joachimth/mk2-reference-loudspeaker/assets/drawings/front_baffle.pdf

## Mk3 Front Baffle —

Cutout & Hole Layout Panel: 300 × 1180 mm, 22 mm birch

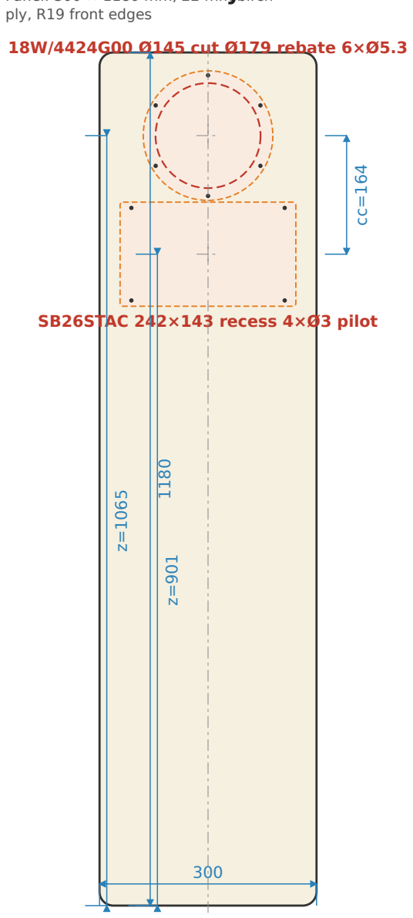
[picture p1: figure]
ply, R19 front edges; 18W/4424G00 Ø145 cut Ø179 rebate 6×Ø5.3; SB26STAC 242×143 recess 4×Ø3 pilot

Red dashed: cutout Orange: rebate Dots: pilot Ø3
