joachimth/mk2-reference-loudspeaker/assets/drawings/mk3-cabinet-drawings.pdf

## Mk3 Cabinet — Assembly Measurement Drawing

### FRONT

### SIDE

12SW

divider 19°

D=420

H=1180 520

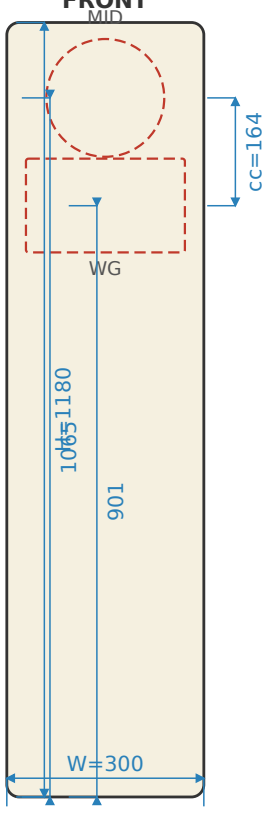
[picture p2: figure]
MID; W=300 H=¹¹⁸⁰ 1065

Internal: 256 × 376 × 1136 mm | Wall: 22 mm | Roundover: R19
Driver heights: MID z=1065 WG/TW z=901 Woofer z=520 | C-C mid/tw:
164 mm Shelf braces at z=[160, 330, 730] | Divider tilt: 19°

## Mk3 Cabinet — Panel Cut List

Material: 22 mm birch plywood | External: 300 × 420 × 1180 mm
Panel | Width (mm) Height/Depth (mm) | Qty | Thickness | Notes
Front baffle | 300 | 1180 | 1 | 22 | R19 front vertical edges, mid + WG cutouts
Back panel | 300 | 1180 | 1 | 22 | Square edges
Side panel L | 420 | 1180 | 1 | 22 | Woofer cutout Ø284, 8×Ø5.5 on Ø319 BCD
Side panel R | 420 | 1180 | 1 | 22 | Woofer cutout Ø284, 8×Ø5.5 on Ø319 BCD (opposed)
Top panel | 300 | 420 | 1 | 22 | Square edges
Bottom panel | 300 | 420 | 1 | 22 | Square edges
Divider plate | 300 | 420 | 1 | 22 | Tilted 19°, cut to fit cavity
Shelf brace 1 | 256 | 376 | 1 | 22 | Ring shelf, rim 45 mm, z=160
Shelf brace 2 | 256 | 376 | 1 | 22 | Ring shelf, rim 45 mm, z=330
Shelf brace 3 | 256 | 376 | 1 | 22 | Ring shelf, rim 45 mm, z=730
Total panels: 10 | Total panel area: 2.37 m² | Plywood volume: 0.05 L
NOTE: Divider plate and shelf braces are cut to fit the internal cavity (256 × 376 mm). Measure
actual internal dims before cutting. All dimensions from cabinet.scad (single source of truth). Verify driver cutouts against datasheet

## Mk3 Front Baffle —

Cutout & Hole Layout Panel: 300 × 1180 mm, 22 mm birch

ply, R19 front edges; 18W/4424G00 Ø145 cut Ø179 rebate 6×Ø5.3; SB26STAC 242×143 recess 4×Ø3 pilot

Red dashed: cutout Orange: rebate Dots: pilot Ø3

## Mk3 Side Panel — Woofer

Cutout & Hole Layout Panel: 420 × 1180 mm, 22 mm birch ply (flat,

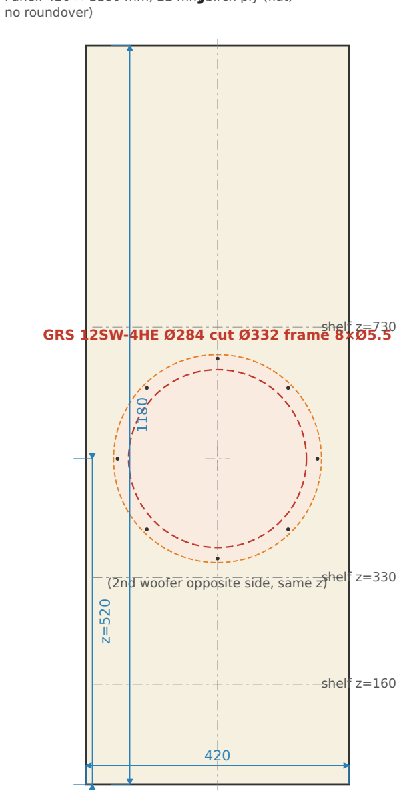
[picture p3: figure]
no roundover); GRS 12SW-4HE Ø284 cut Ø332 frame 8×Ø5.5; (2nd woofer opposite side, same z); shelf z=160; shelf z=330; shelf z=730

## Front Baffle — Cut

Drawing 300 × 1180 mm, 22 mm ply, R19 front edges

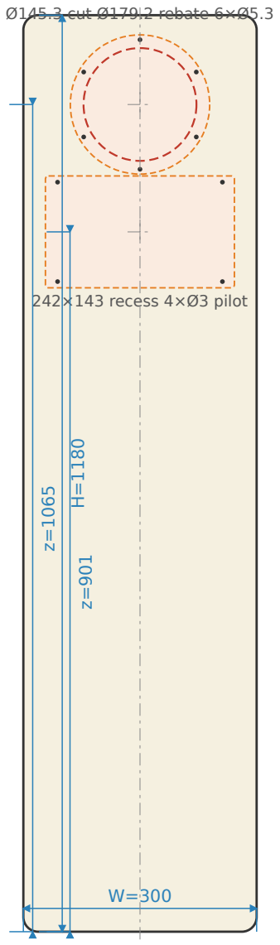
[picture p4: figure]
Ø145.3 cut Ø179.2 rebate 6×Ø5.3; 242×143 recess 4×Ø3 pilot

## Back Panel — Cut

Drawing 300 × 1180 mm, 22 mm ply, square edges

W=300

H=1180 No cutouts

## Side Panel LEFT — Cut

Drawing 420 × 1180 mm, 22 mm ply, woofer on left face

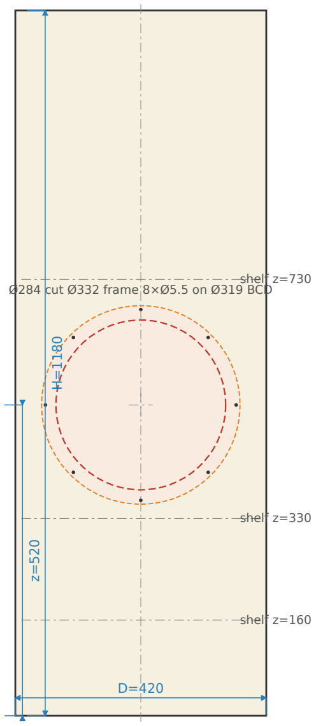
[picture p5: figure]
Ø284 cut Ø332 frame 8×Ø5.5 on Ø319 BCD; shelf z=160; shelf z=330; shelf z=730

## Side Panel RIGHT — Cut

Drawing 420 × 1180 mm, 22 mm ply, woofer on right (opposed) face

## Top Panel — Cut Drawing

300 × 420 mm, 22 mm ply, R19 front
edge

W=300

D=420 No cutouts

## Bottom Panel — Cut

Drawing 300 × 420 mm, 22 mm ply, R19 front edge

W=300

D=420 No cutouts

## Divider Plate — Cut

Drawing 256 × 376 mm, 22 mm ply, tilted 19° in cabinet

Cut to internal cavity shape (front edge follows rounded side walls)

Front edge sits at z=985 mm, rises 19° toward rear

int W=256 int D=³⁷⁶

tilt 19°

## Shelf Brace ×3 — Cut

Drawing Outer: 256 × 376 mm (internal cavity) Rim: 45 mm Thickness: 22 mm Qty: 3 (z=[160, 330, 730])

Open centre
166 × 286 mm

outer 256 outer 376

inner 166

## Skæreplan — massiv fyr 25 mm (Jem & Fix) — ET PAR

5× 620×2420×25 mm | 300×420×1180 mm | 2 kabinetter (V+H)

Side L (V)
420×1180 mm

Side L (H)
420×1180 mm

spild
60 mm

reserve
200 mm

Plade 1
sider V

Side R (V)
420×1180 mm

Side R (H)
420×1180 mm

spild
60 mm

reserve
200 mm

Plade 2
sider H

Front (V)
300×1180 mm

Front (H)
300×1180 mm

spild
60 mm

Divider (V)
trim→250×370

Hylde 1 (V)
trim→250×370

Hylde 2 (V)
trim→250×370

Hylde 3 (V)
trim→250×370

reserve
940 mm

Plade 3
front + div V + hylder V

Bagplade (V)
300×1180 mm

Bagplade (H)
300×1180 mm

spild
60 mm

Divider (H)
trim→250×370

Hylde 1 (H)
trim→250×370

Hylde 2 (H)
trim→250×370

Hylde 3 (H)
trim→250×370

reserve
940 mm

Plade 4
bagplade + div H + hylder H

Toplåg (V)
300×420 mm

Bundplade (V)
300×420 mm

Toplåg (H)
300×420 mm

Bundplade (H)
300×420 mm

reserve
740 mm

reserve
320 mm

Plade 5
toplåg + bund
Bruges | Reserve/spild | Rip-snit (orange)
