joachimth/mk2-reference-loudspeaker/assets/drawings/panel_front_baffle.pdf

## Front Baffle — Cut

Drawing 300 × 1180 mm, 22 mm ply, R19 front edges

Ø145.3 cut Ø179.2 rebate 6×Ø5.3; 242×143 recess 4×Ø3 pilot
