joachimth/mk2-reference-loudspeaker/assets/mk2_estimeret_respons.png

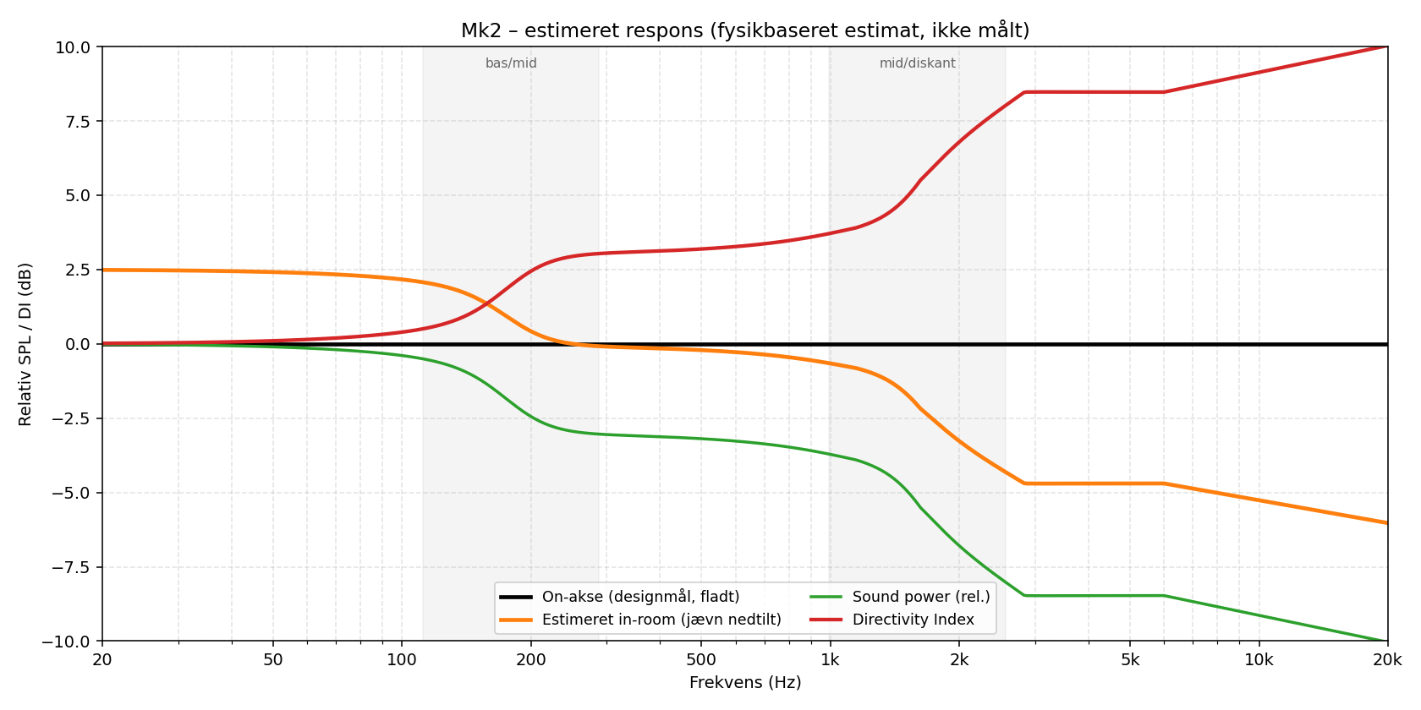
assets/mk2_estimeret_respons.png
