joachimth/mk2-reference-loudspeaker/assets/mk2_kabinet_tegning.png

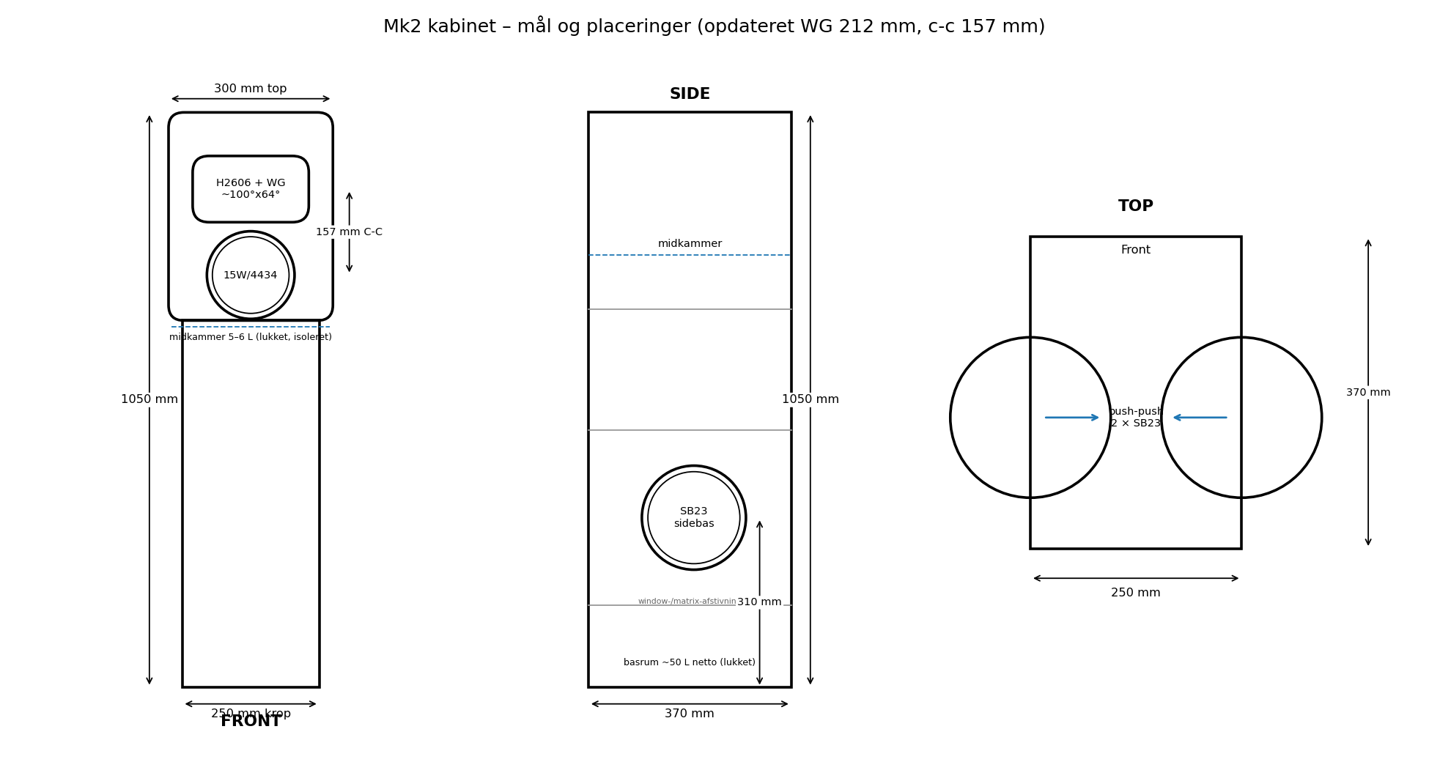
assets/mk2_kabinet_tegning.png
