joachimth/mk2-reference-loudspeaker/assets/renders/baffel_insert_fit_front.png

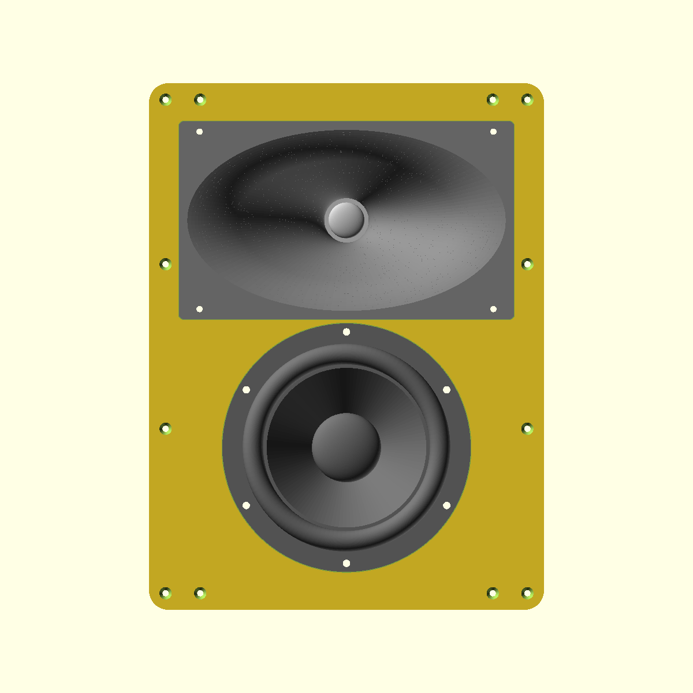
assets/renders/baffel_insert_fit_front.png
