joachimth/mk2-reference-loudspeaker/assets/renders/baffel_insert_fit_rear.png

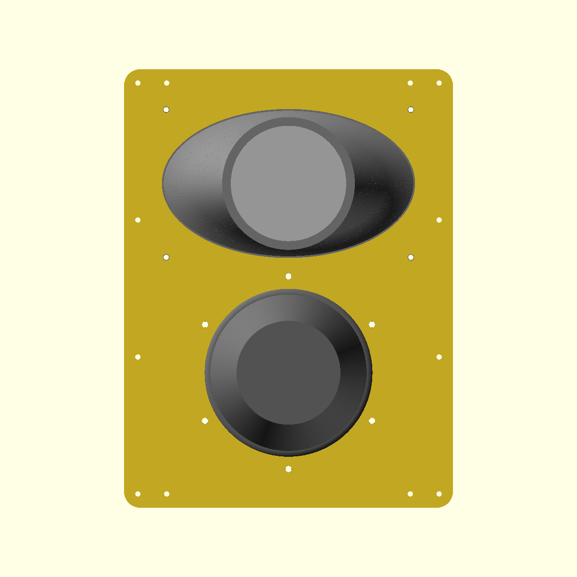
assets/renders/baffel_insert_fit_rear.png
