joachimth/mk2-reference-loudspeaker/assets/renders/baffel_insert_front.png

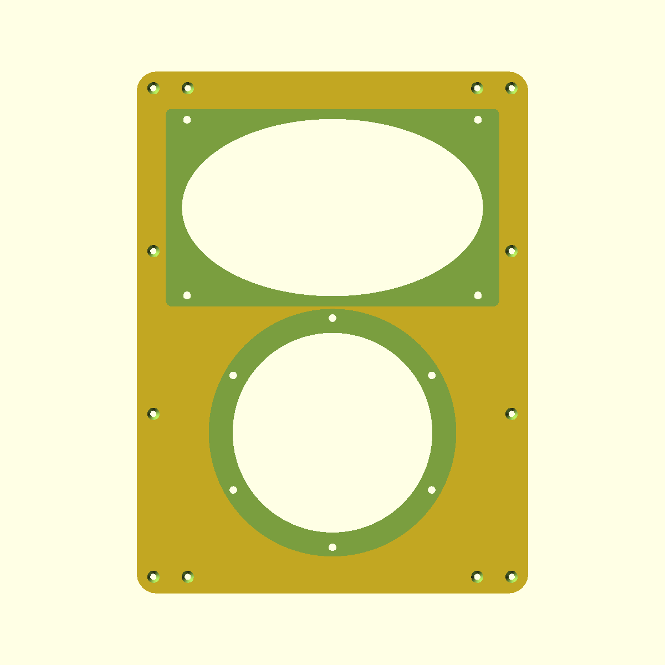
assets/renders/baffel_insert_front.png
