joachimth/mk2-reference-loudspeaker/assets/renders/cabinet_cutaway.png

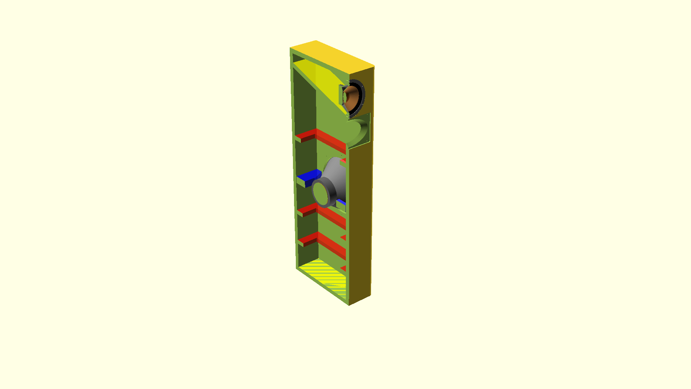
assets/renders/cabinet_cutaway.png
