joachimth/mk2-reference-loudspeaker/simulations/plots/bass_alignment_maxspl.png

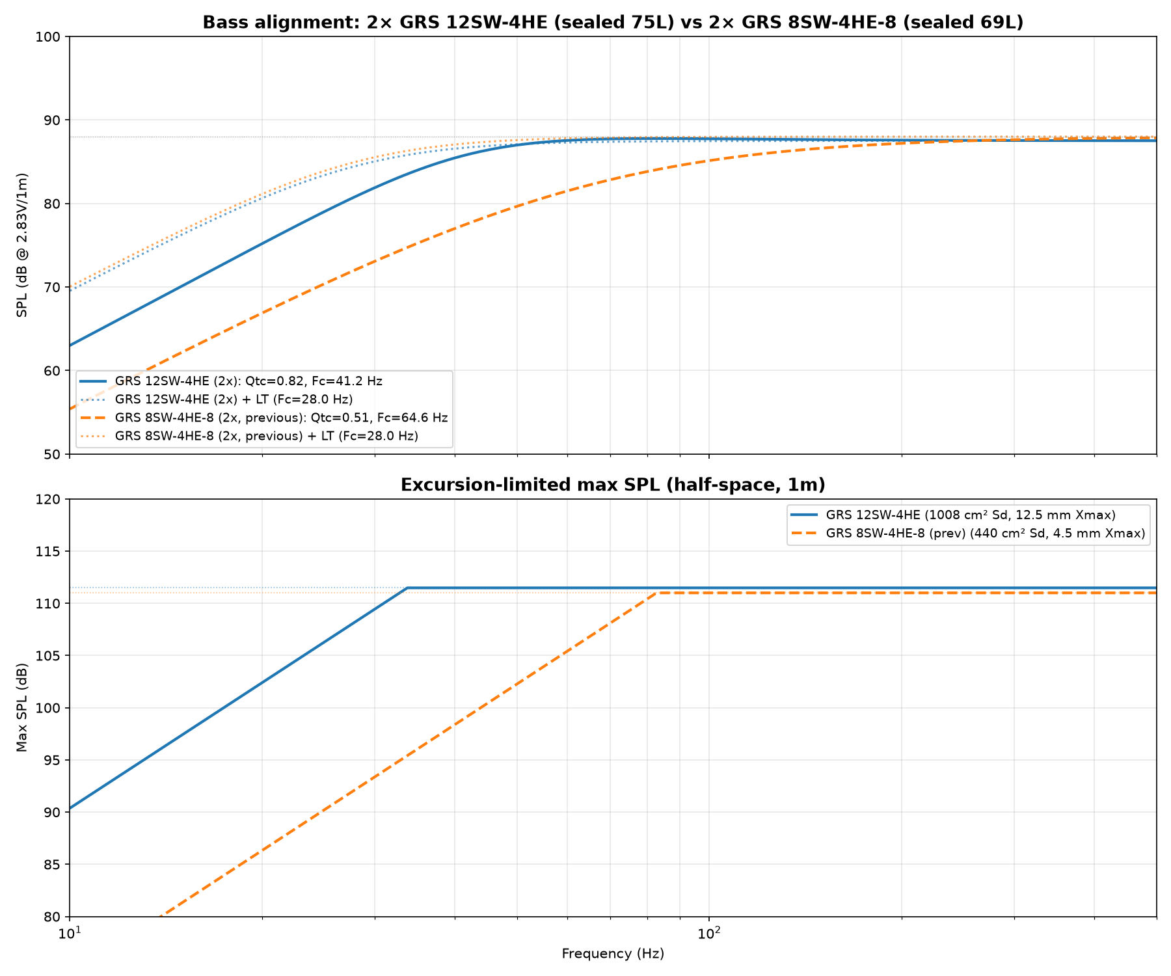
simulations/plots/bass_alignment_maxspl.png
