joachimth/mk2-reference-loudspeaker/simulations/plots/bass_volume_compare.png

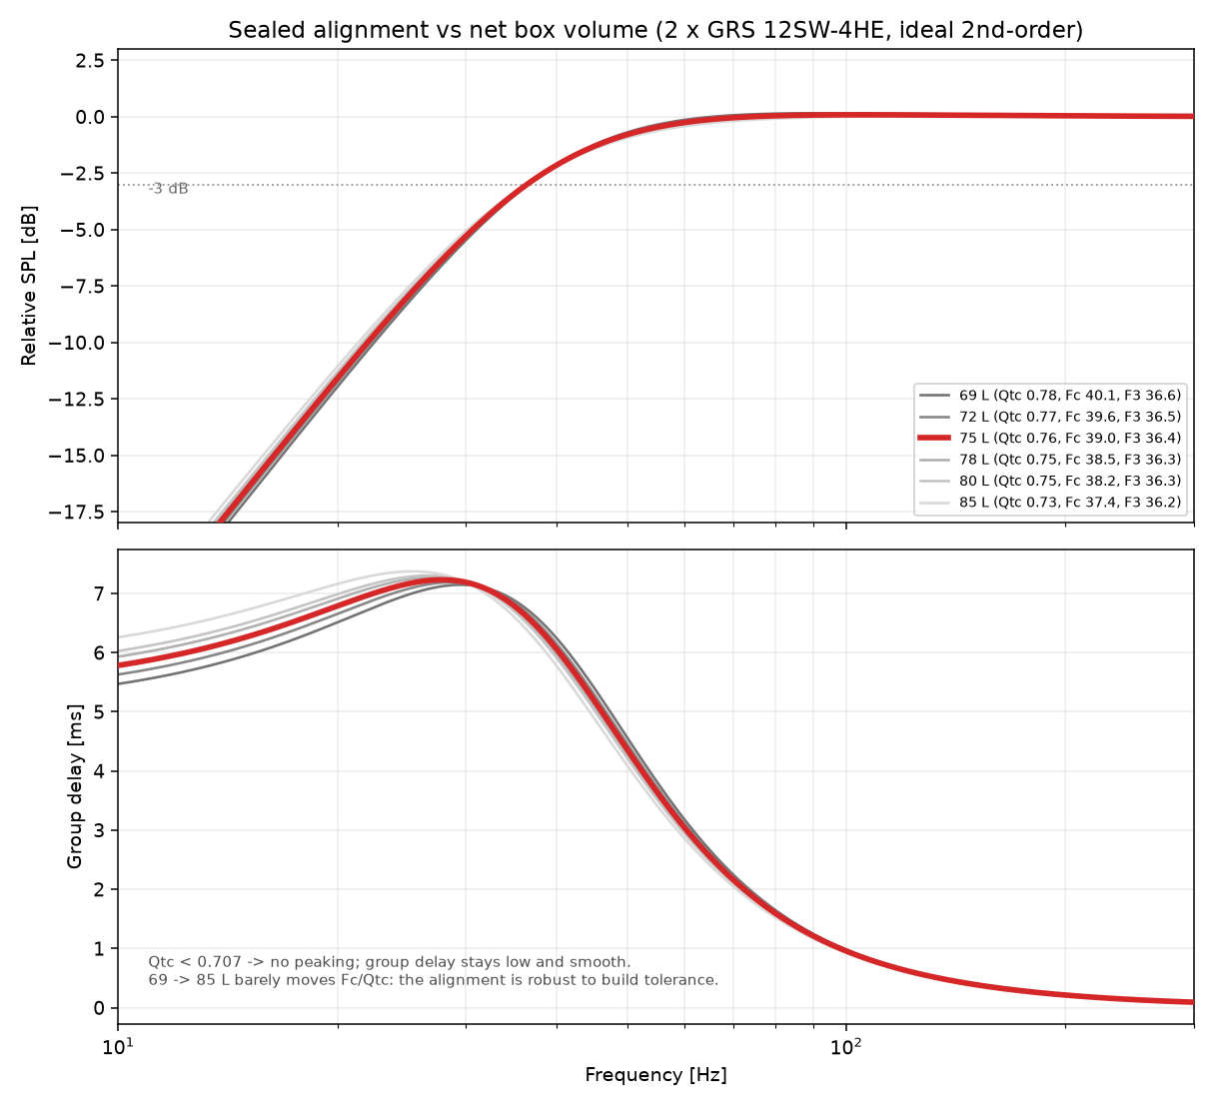
simulations/plots/bass_volume_compare.png
