joachimth/mk2-reference-loudspeaker/simulations/plots/breakin_projection.png

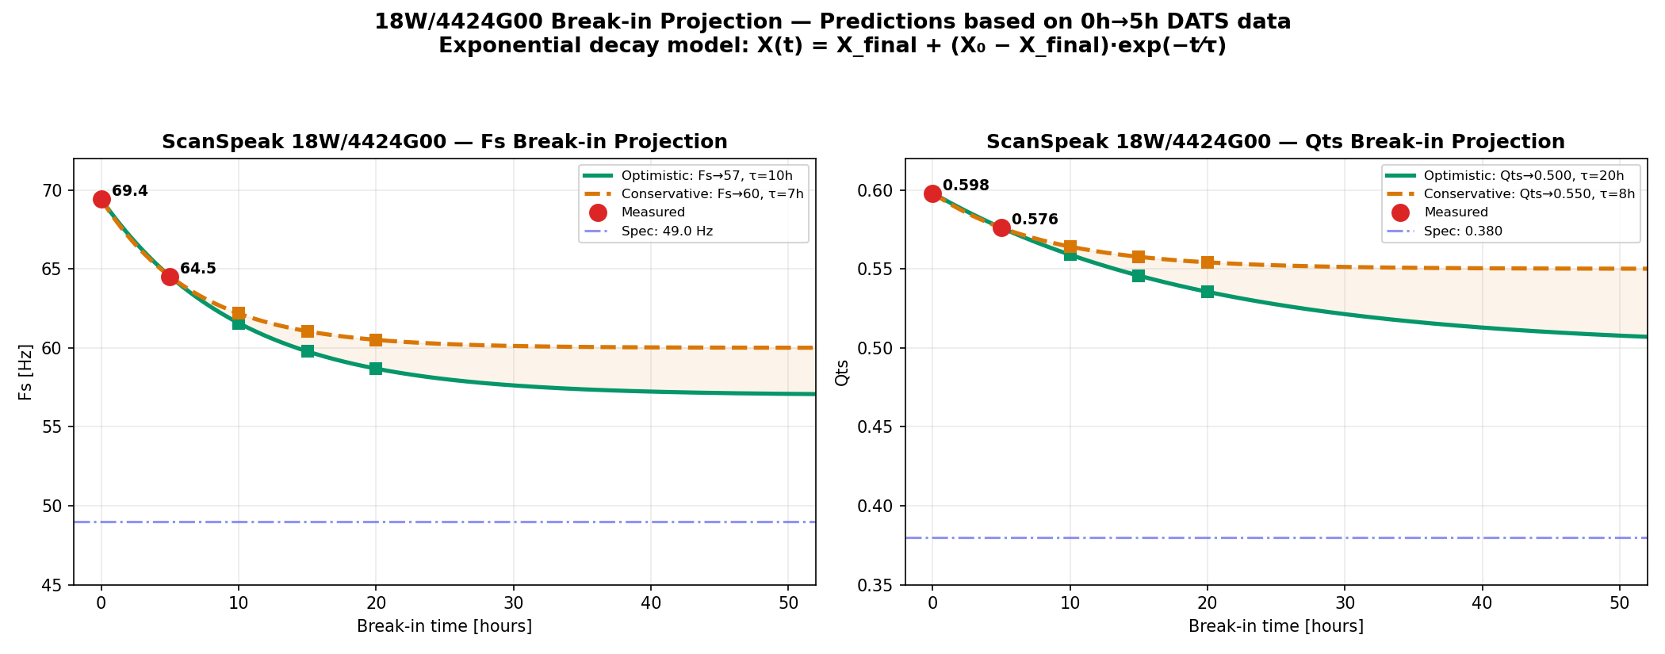
simulations/plots/breakin_projection.png
