joachimth/mk2-reference-loudspeaker/simulations/plots/crossover_optimization.png

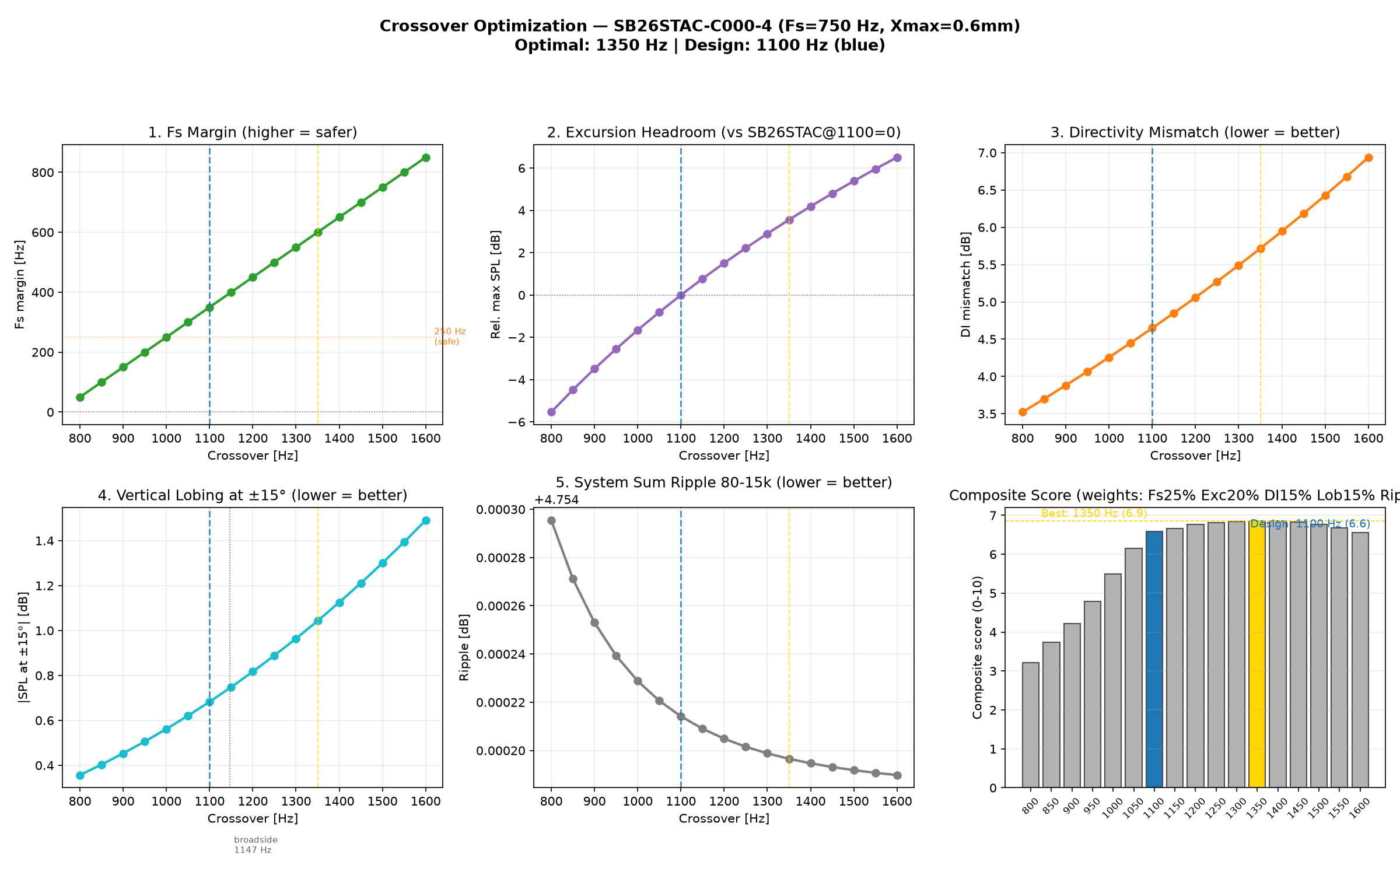
simulations/plots/crossover_optimization.png
