joachimth/mk2-reference-loudspeaker/simulations/plots/crossover_woofer_mid.png

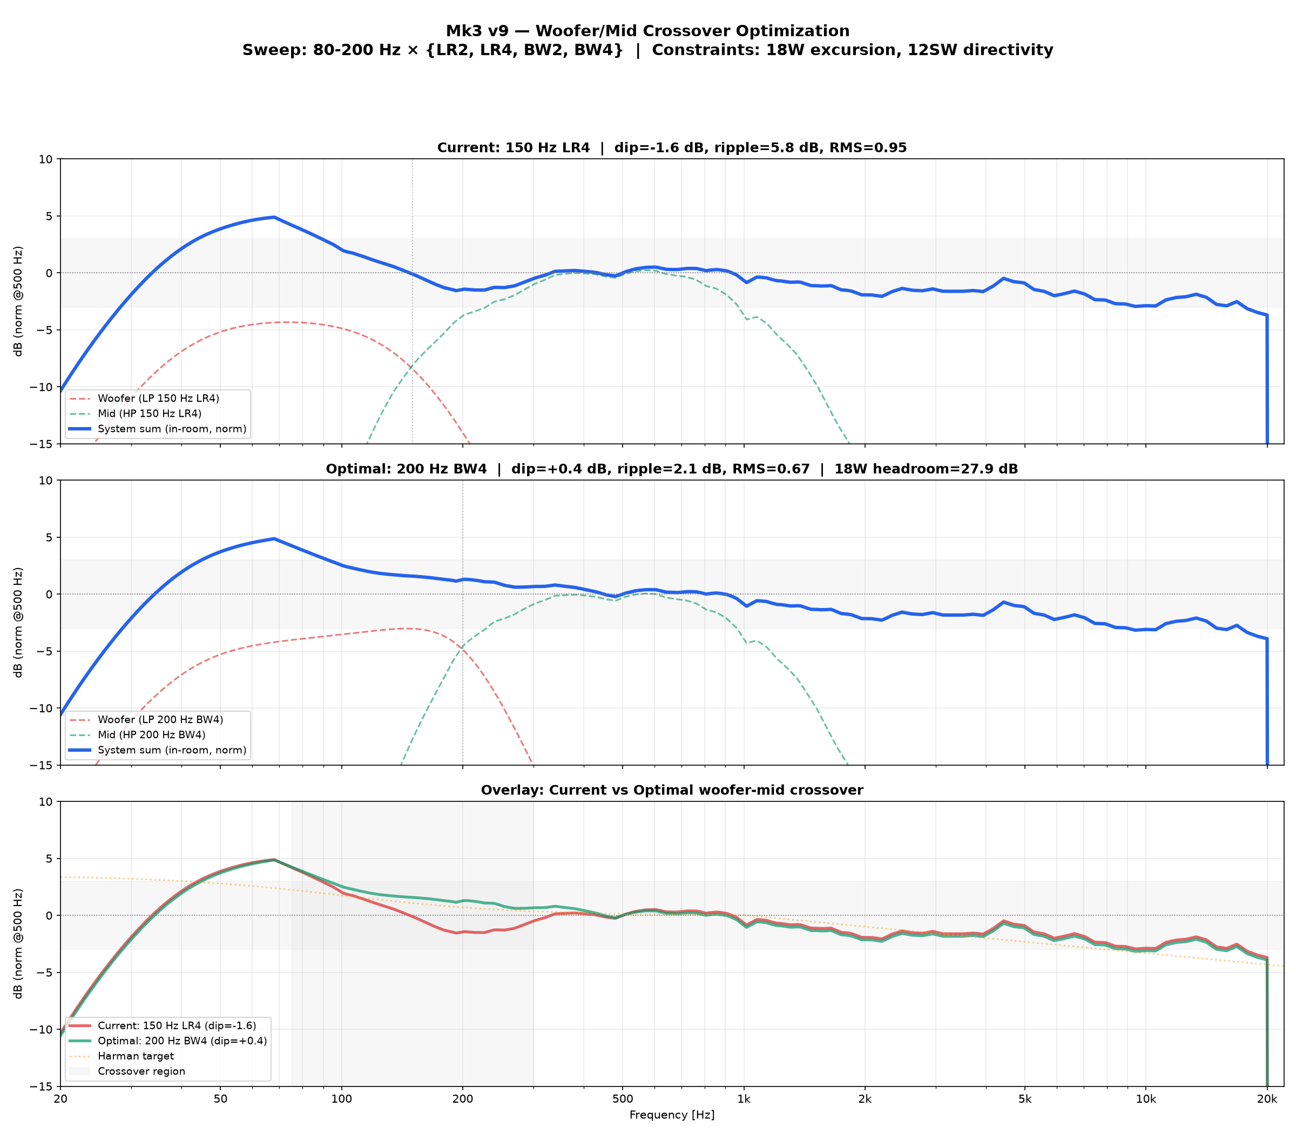
simulations/plots/crossover_woofer_mid.png
