joachimth/mk2-reference-loudspeaker/simulations/plots/dats_vs_datasheet_bass.png

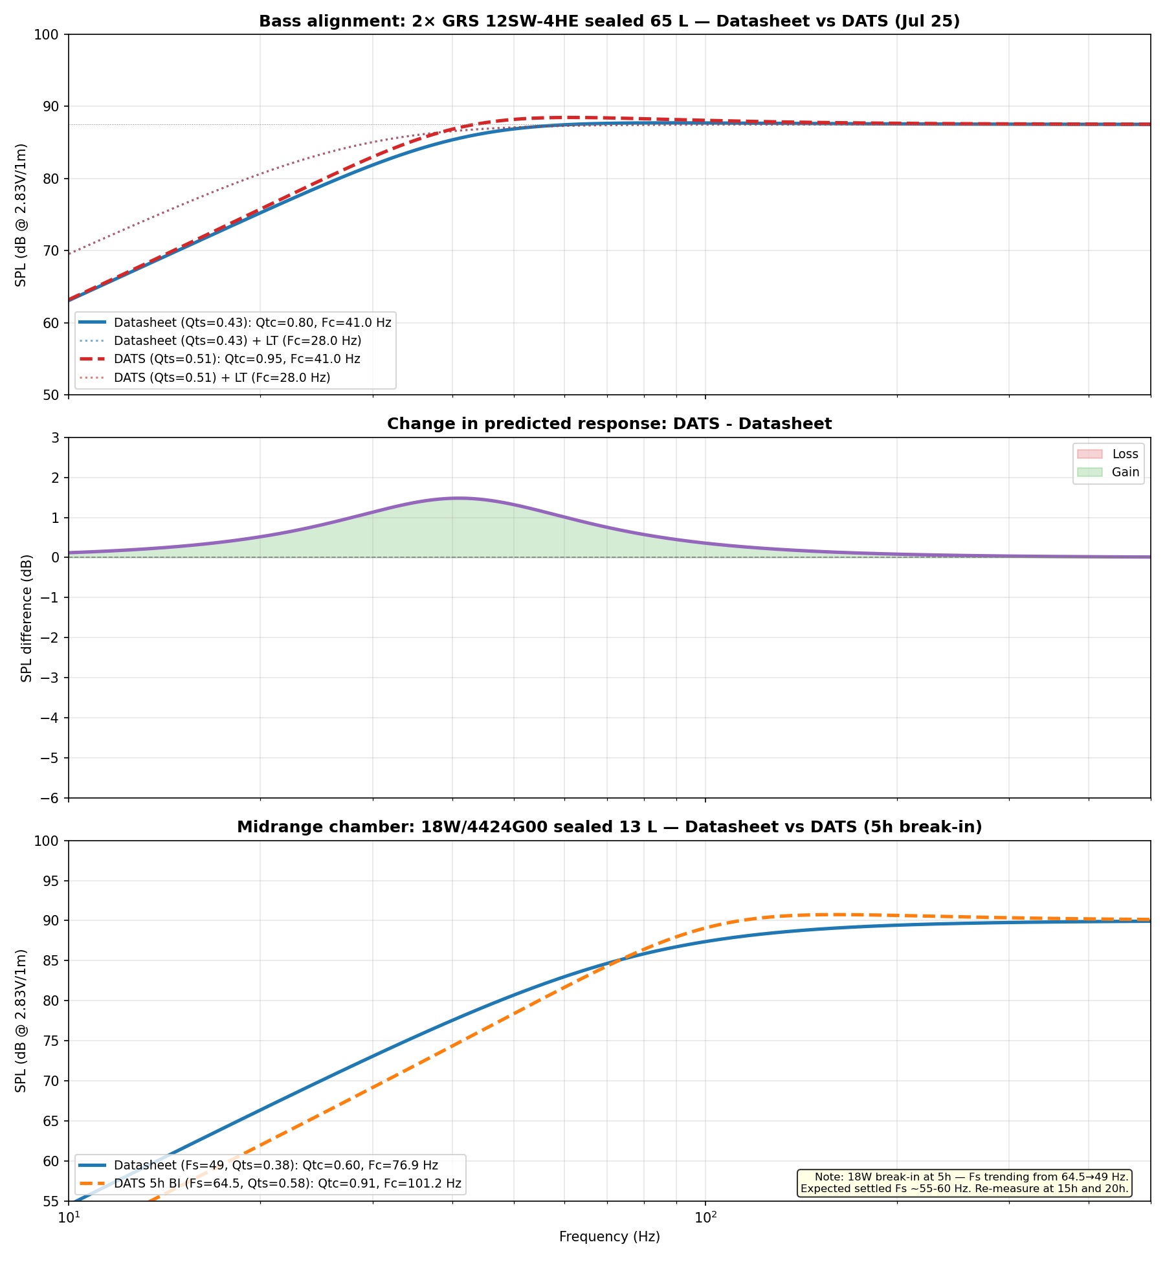
simulations/plots/dats_vs_datasheet_bass.png
