joachimth/mk2-reference-loudspeaker/simulations/plots/dats_vs_datasheet_full.png

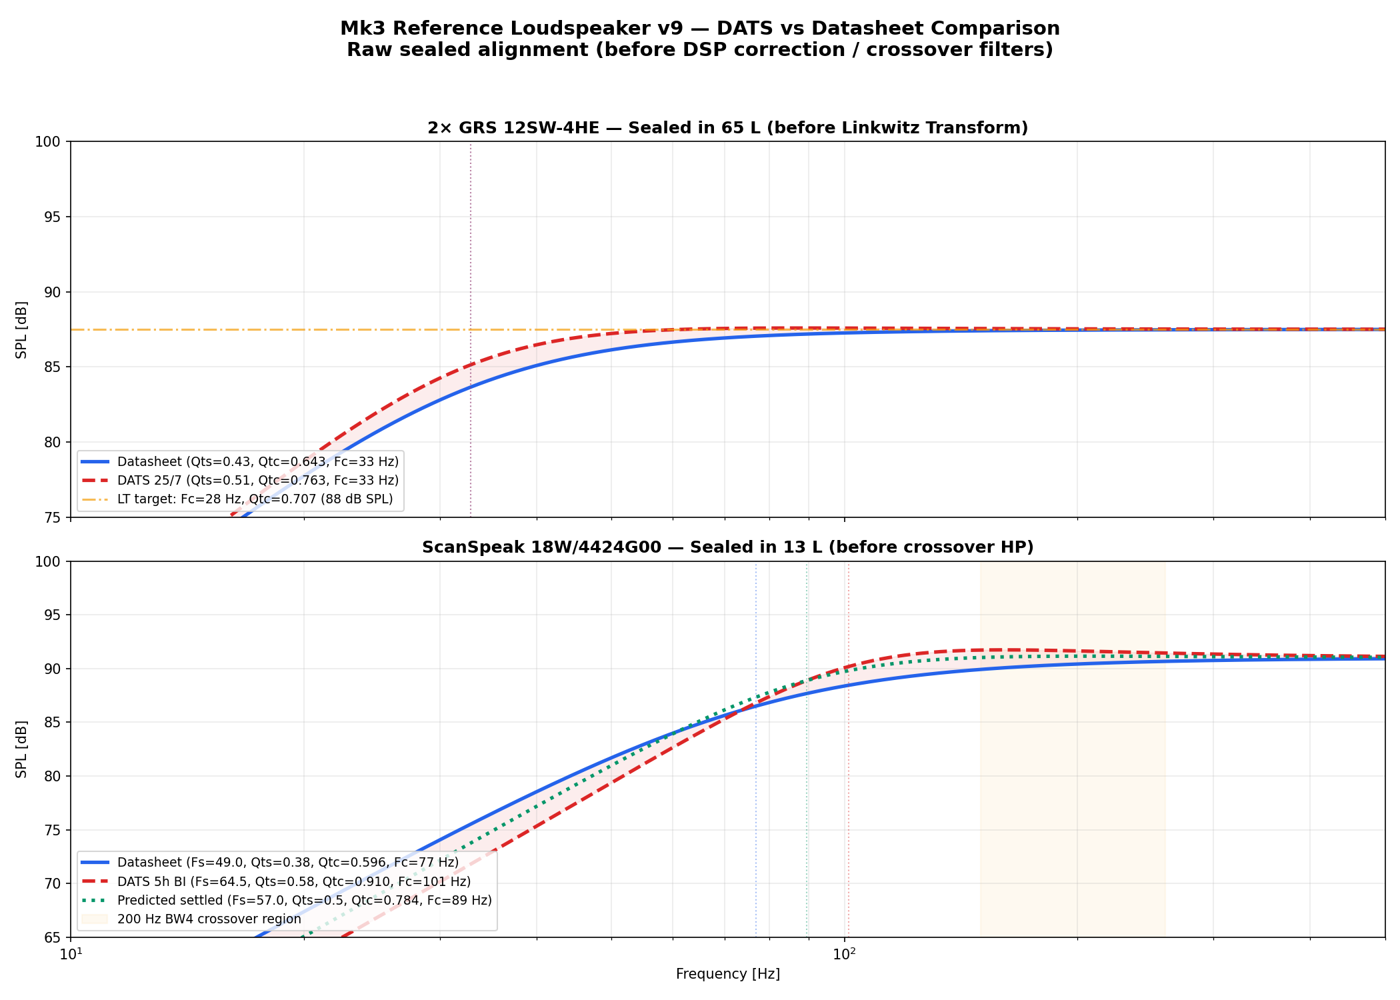
simulations/plots/dats_vs_datasheet_full.png
