joachimth/mk2-reference-loudspeaker/simulations/plots/directivity_estimate.png

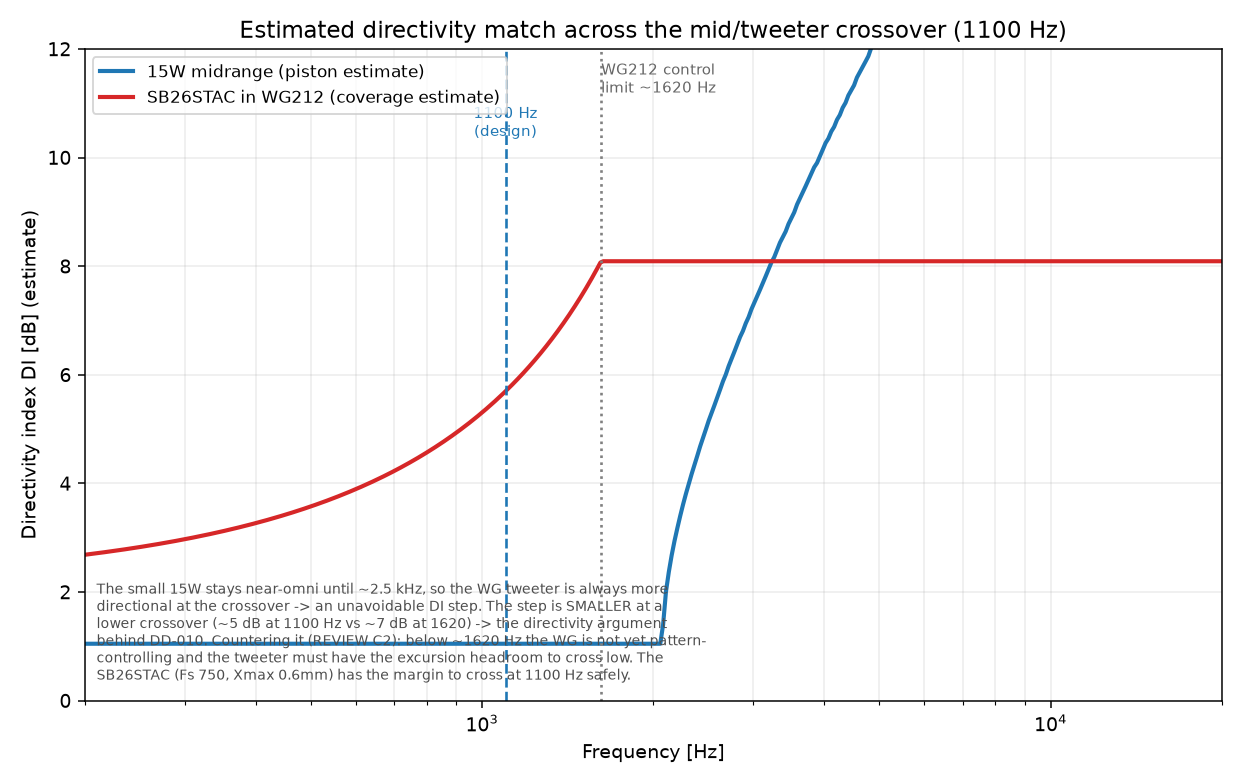
simulations/plots/directivity_estimate.png
