joachimth/mk2-reference-loudspeaker/simulations/plots/inroom_gain_optimization.png

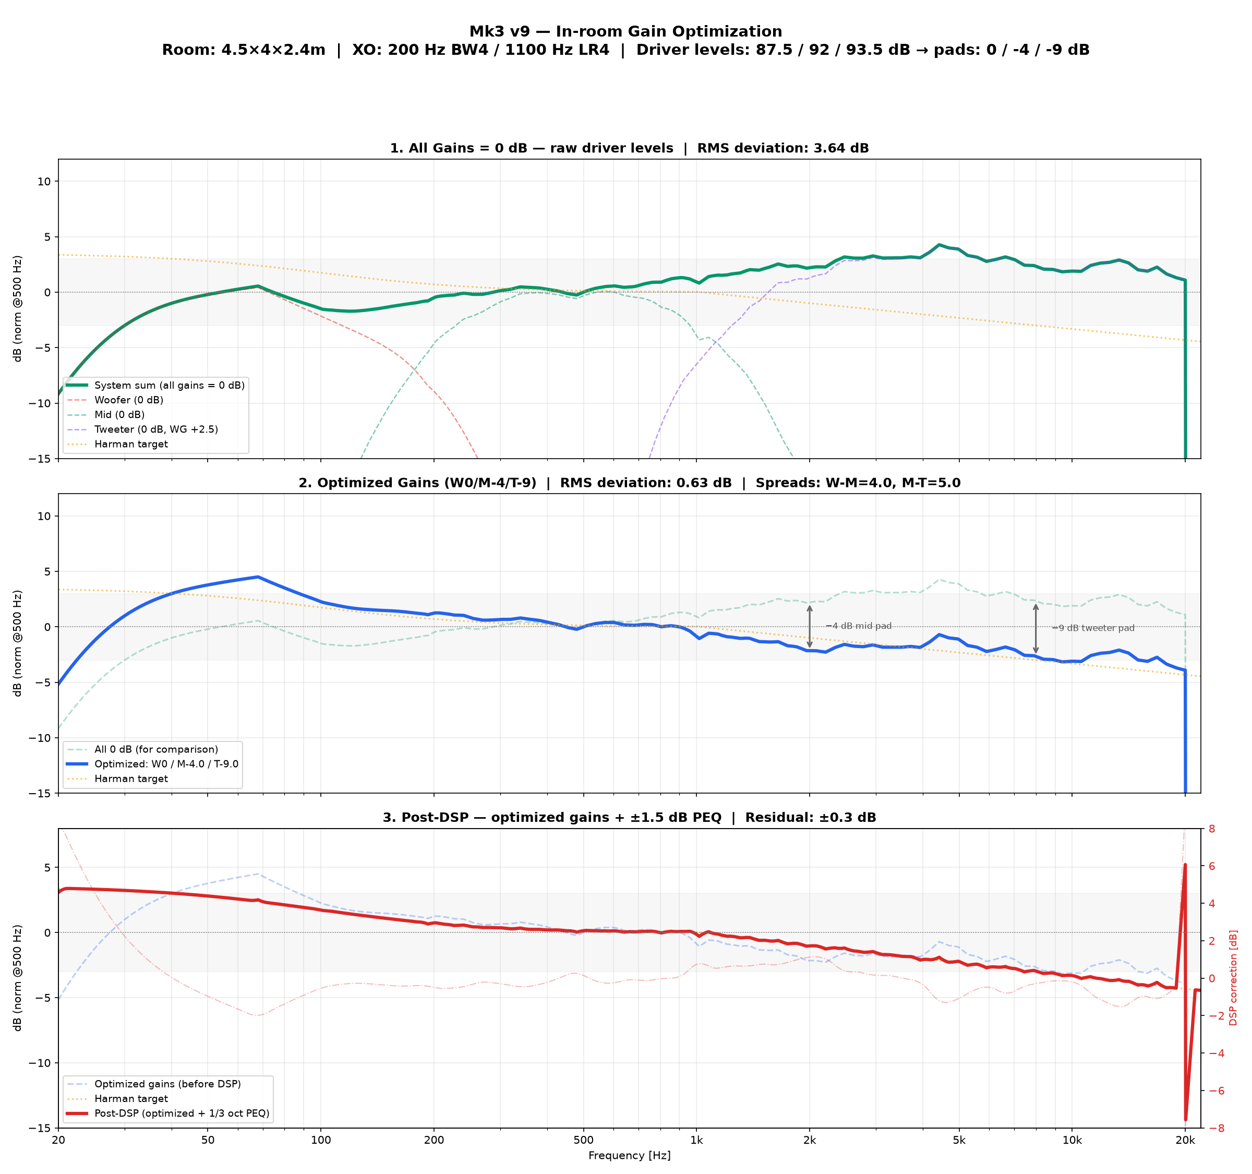
simulations/plots/inroom_gain_optimization.png
