joachimth/mk2-reference-loudspeaker/simulations/plots/optimal_response.png

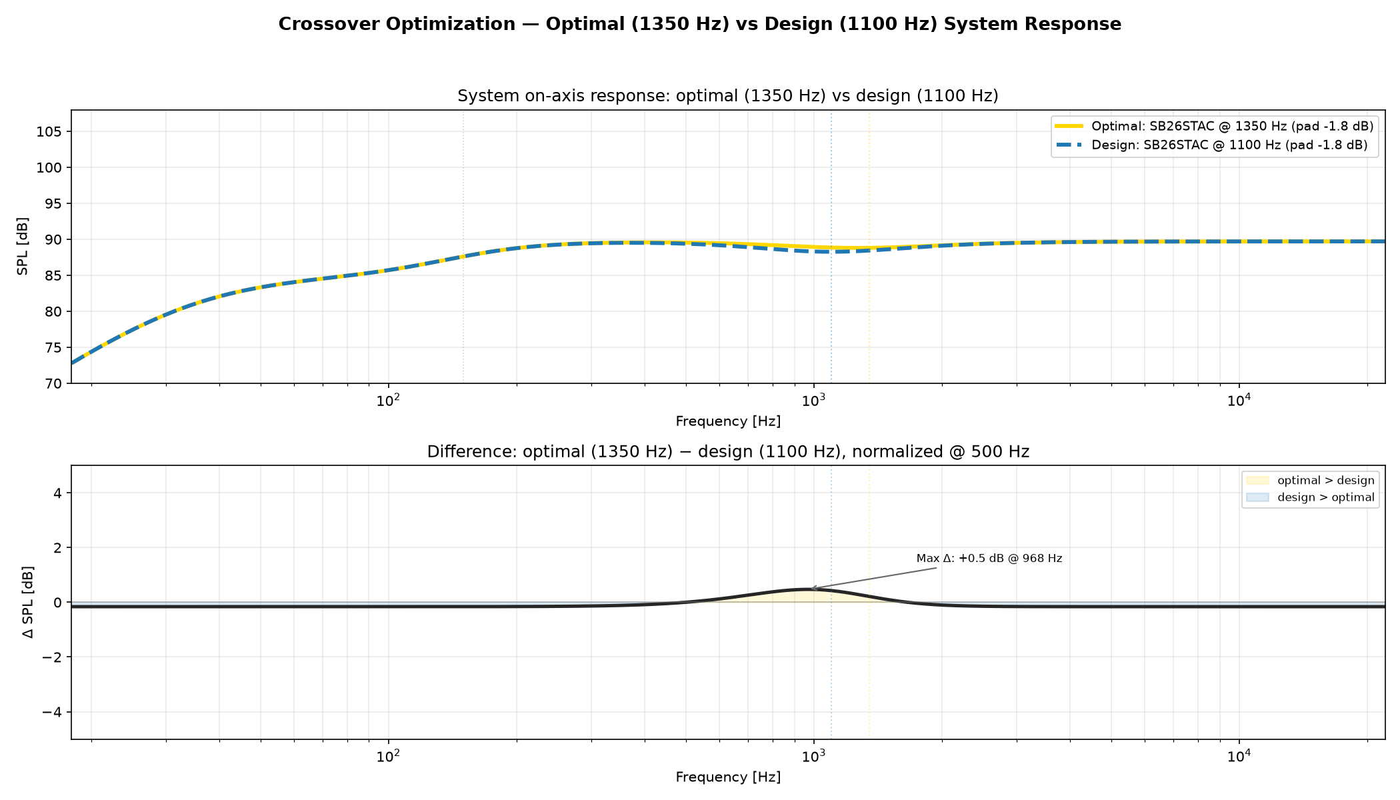
simulations/plots/optimal_response.png
