joachimth/mk2-reference-loudspeaker/simulations/plots/polar_response.png

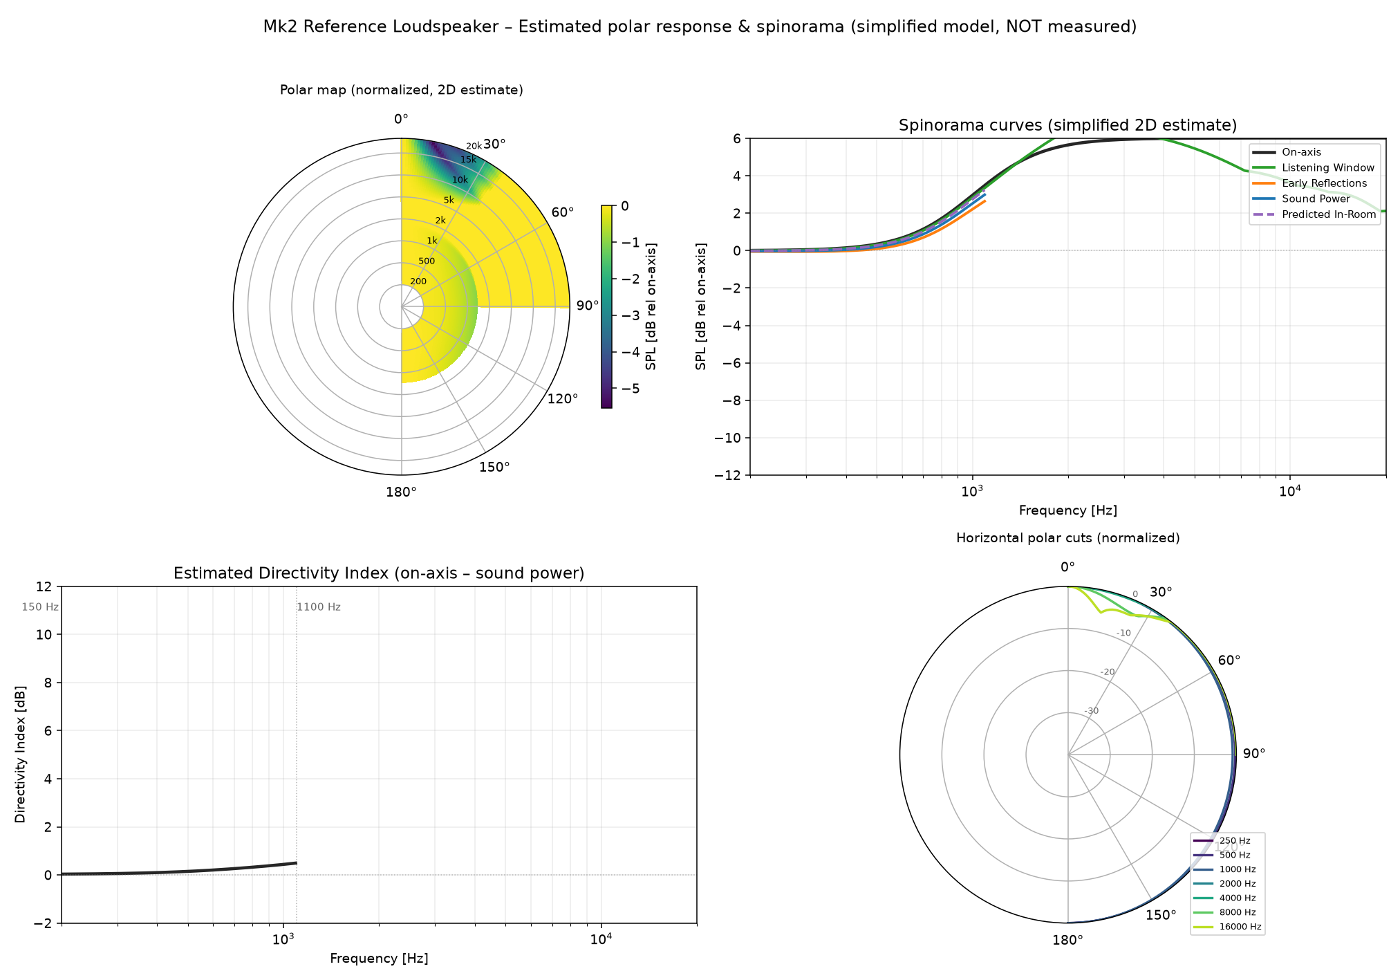
simulations/plots/polar_response.png
