joachimth/mk2-reference-loudspeaker/simulations/plots/spinorama_estimate.png

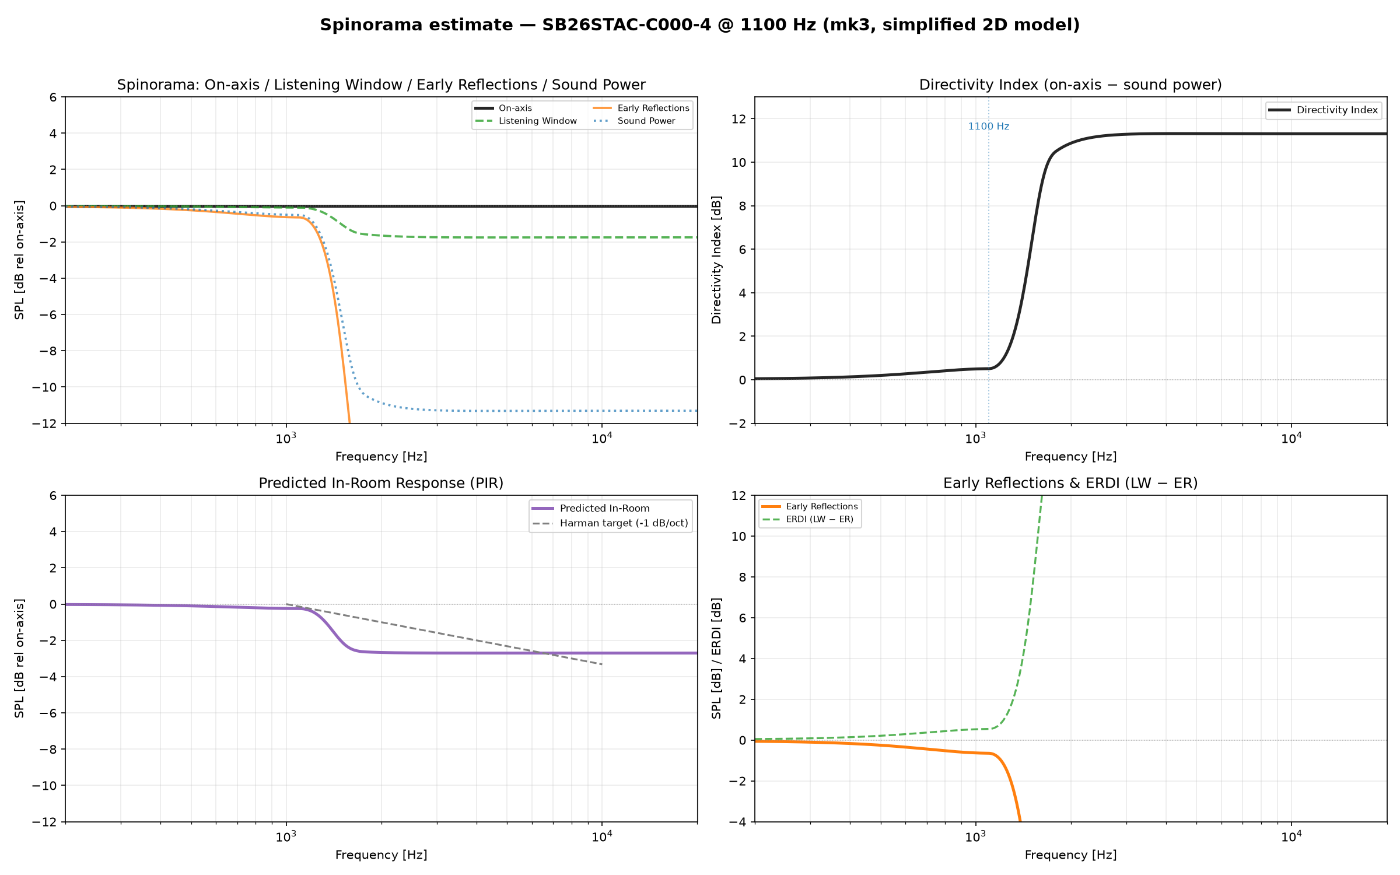
simulations/plots/spinorama_estimate.png
