joachimth/mk2-reference-loudspeaker/simulations/plots/system_response_anechoic.png

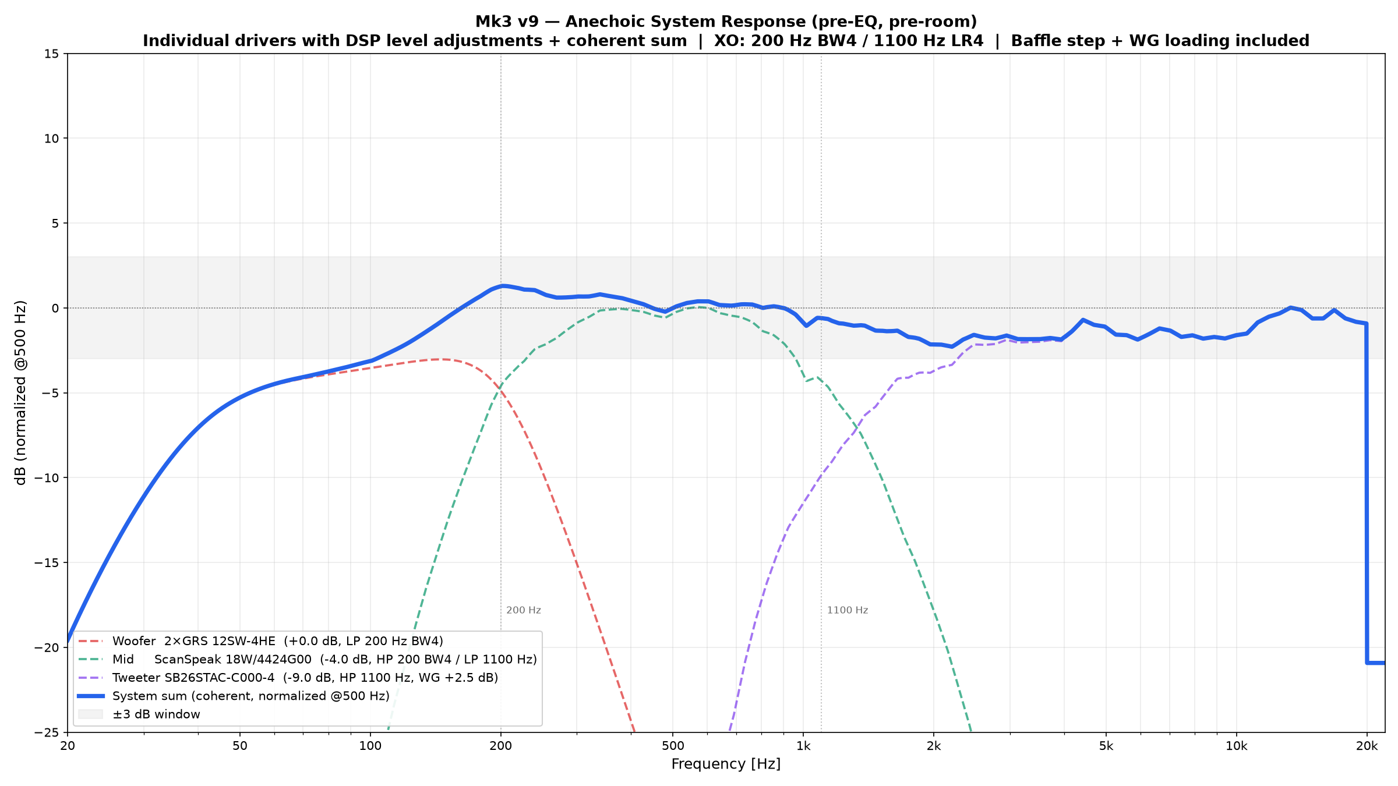
simulations/plots/system_response_anechoic.png
