joachimth/mk2-reference-loudspeaker/simulations/plots/system_response_inroom.png

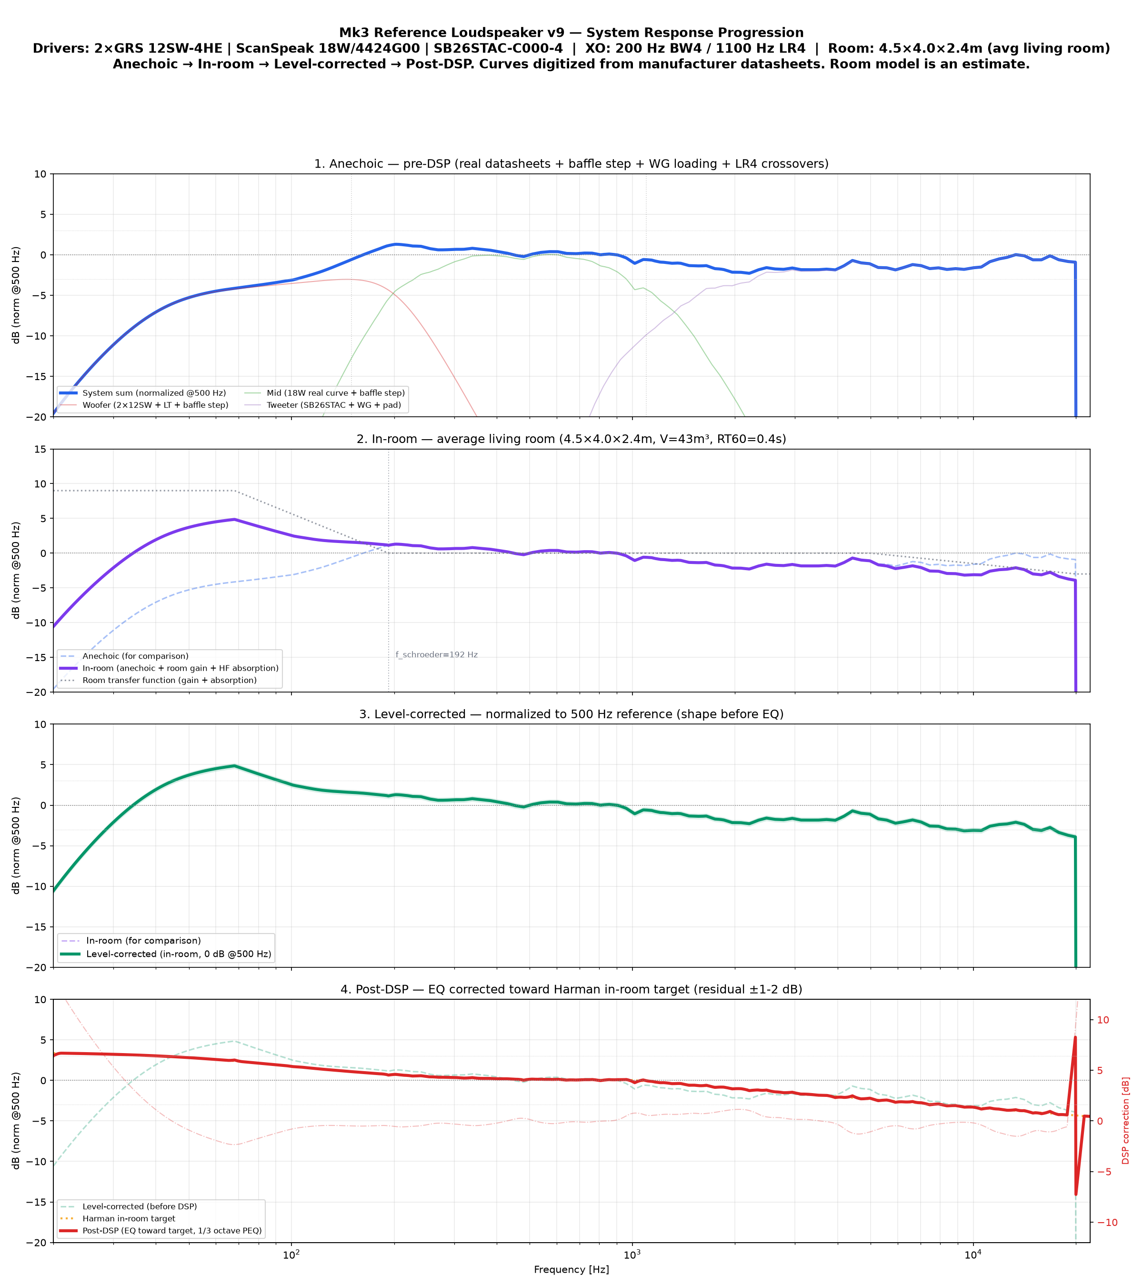
simulations/plots/system_response_inroom.png
