joachimth/mk2-reference-loudspeaker/simulations/plots/system_response_realistic.png

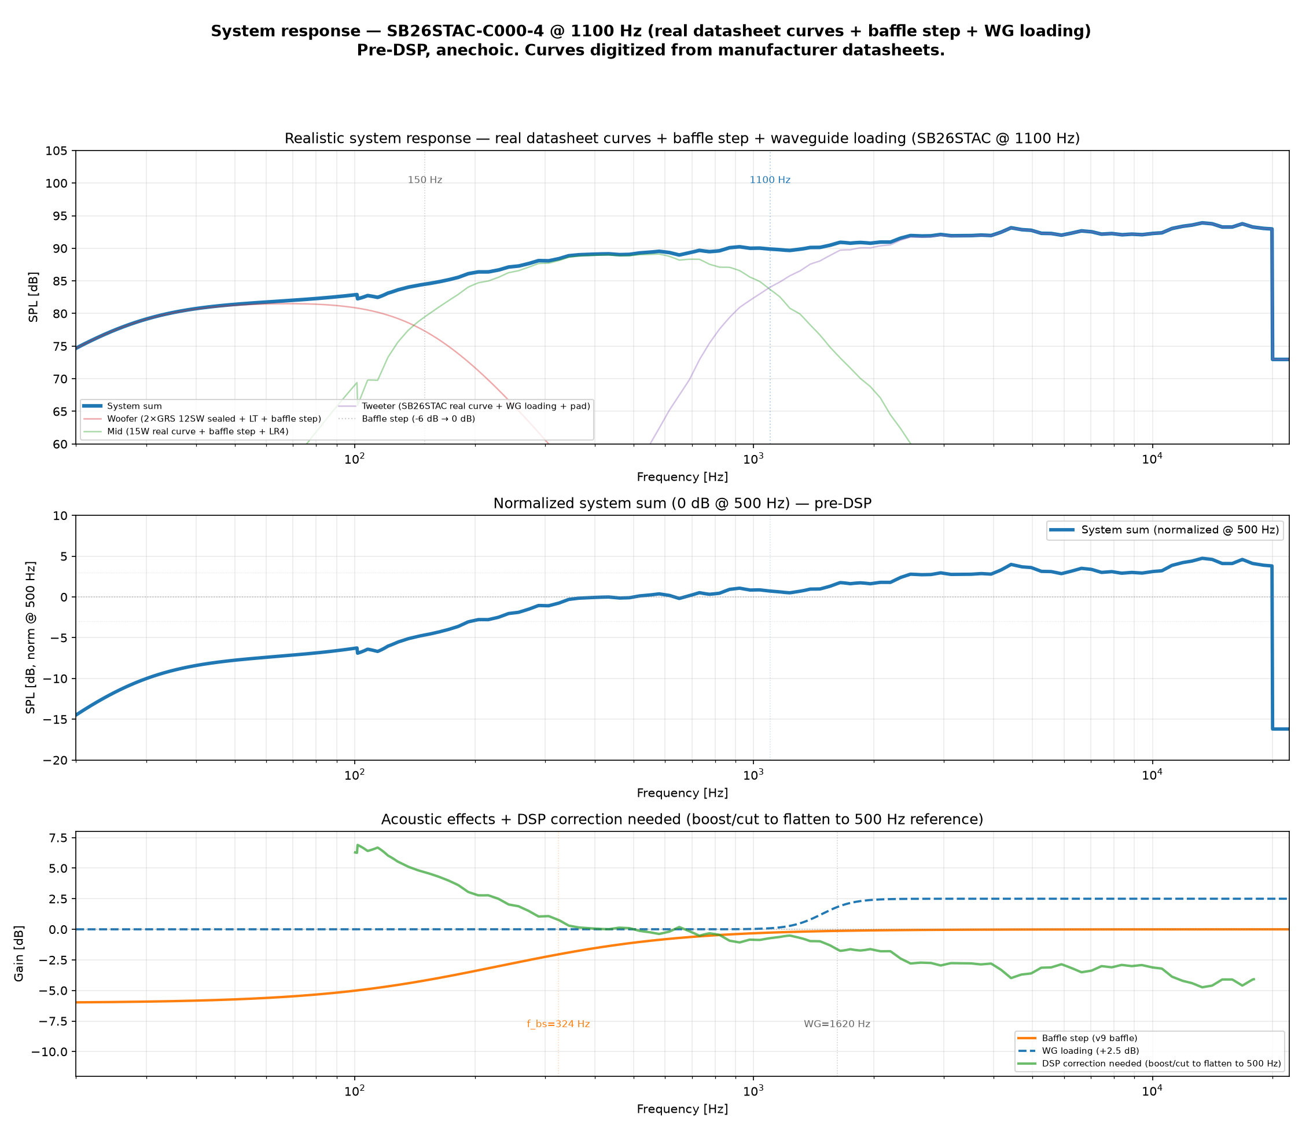
simulations/plots/system_response_realistic.png
