joachimth/mk2-reference-loudspeaker/simulations/plots/target_comparison.png

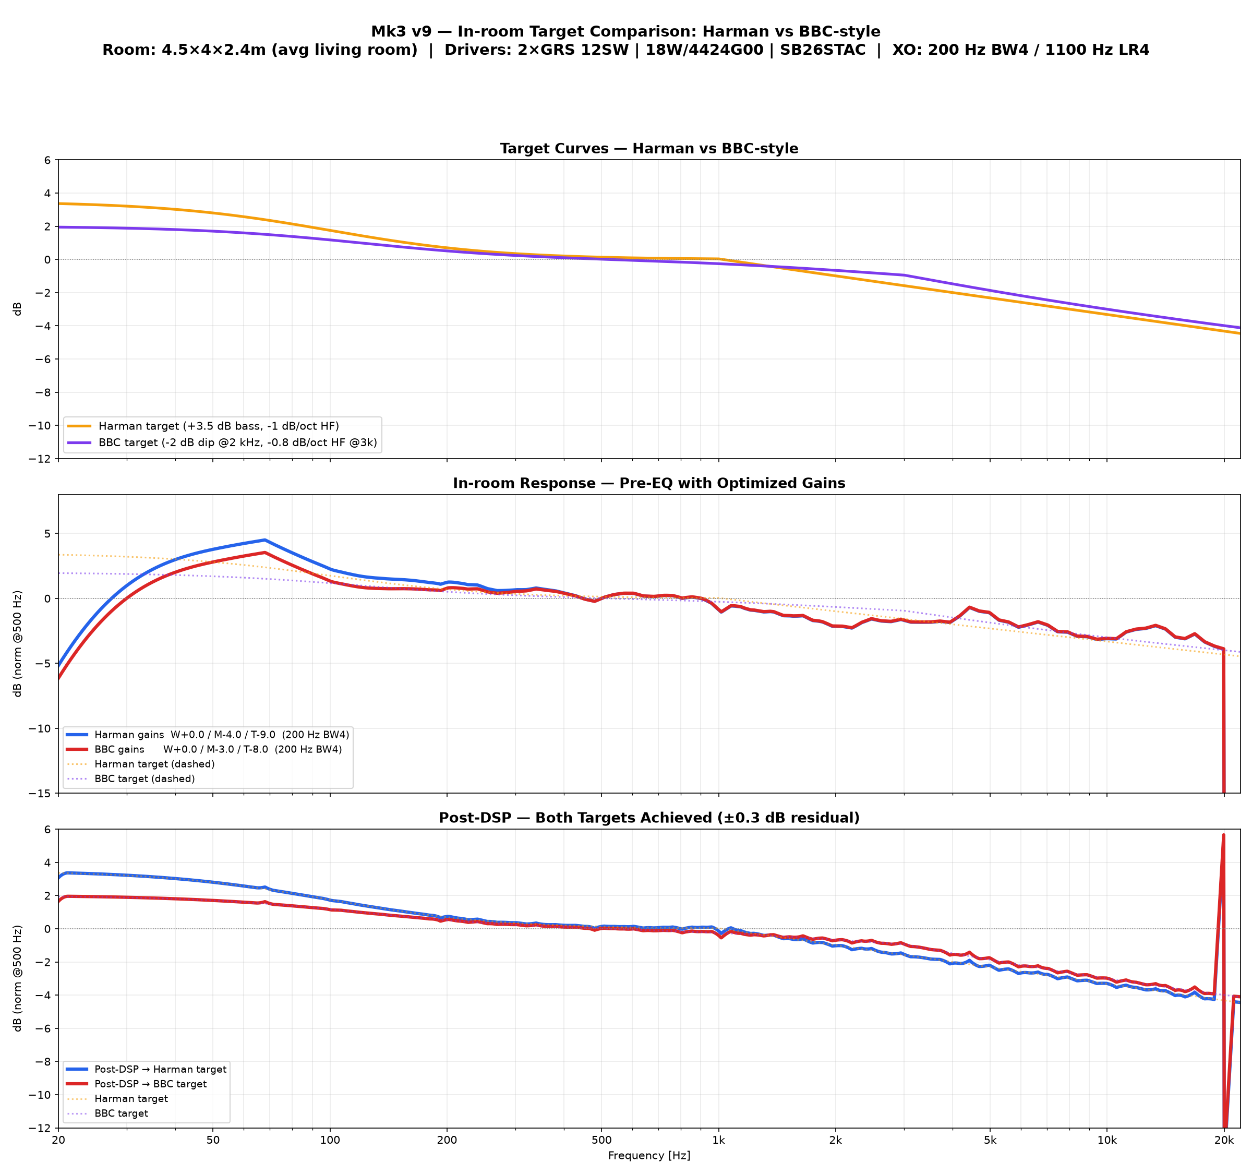
simulations/plots/target_comparison.png
