joachimth/mk2-reference-loudspeaker/simulations/plots/tweeter_comparison.png

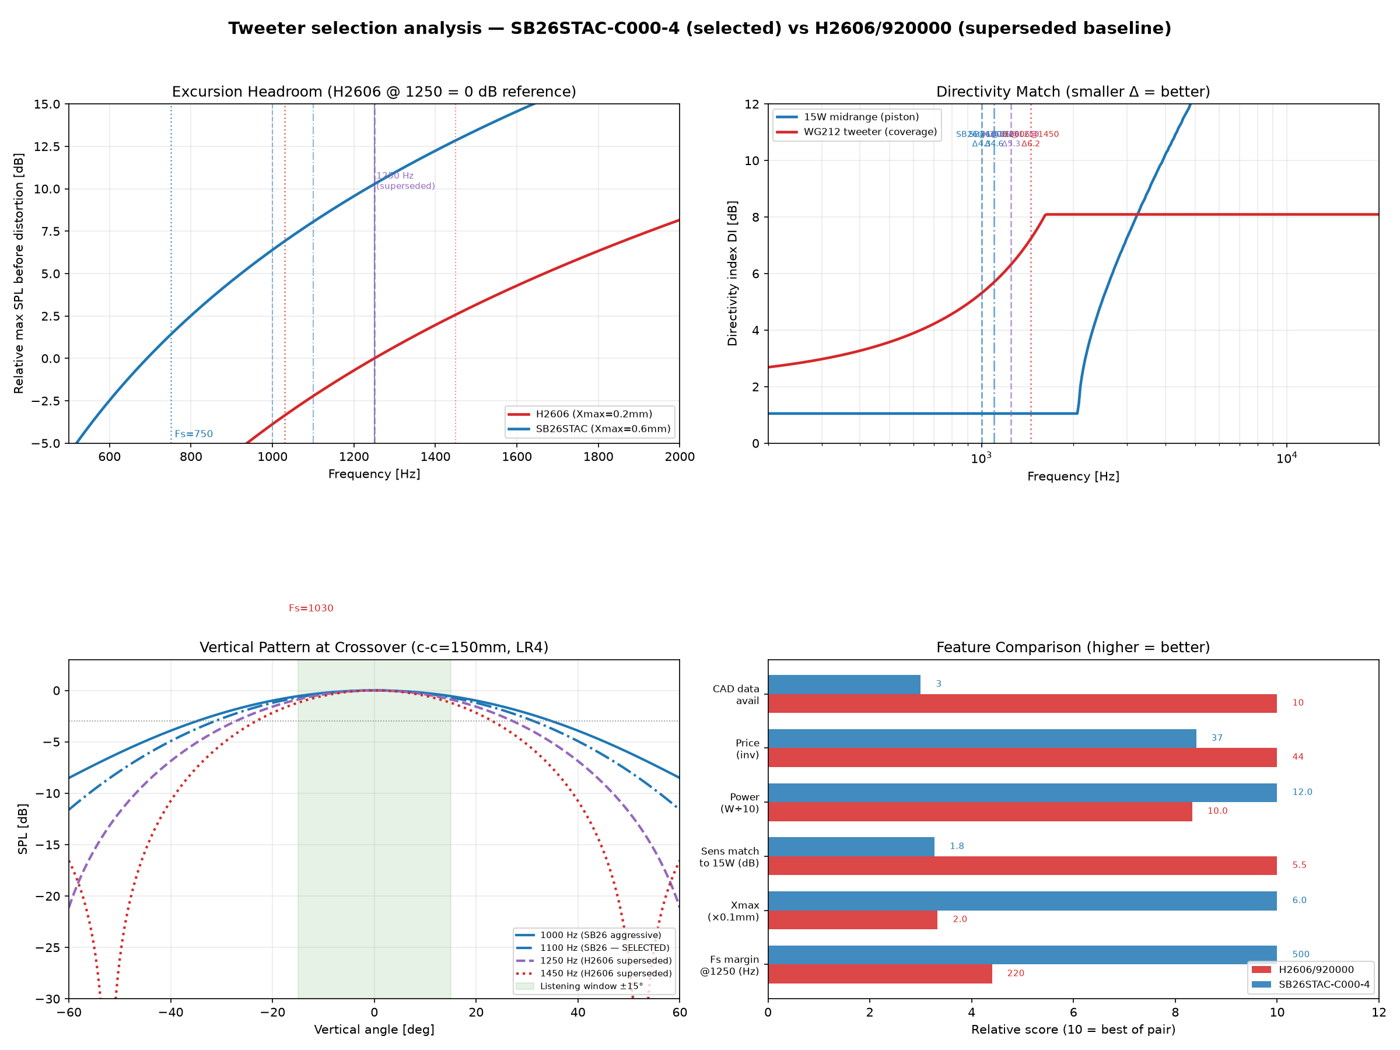
simulations/plots/tweeter_comparison.png
