joachimth/mk2-reference-loudspeaker/simulations/plots/vertical_lobing.png

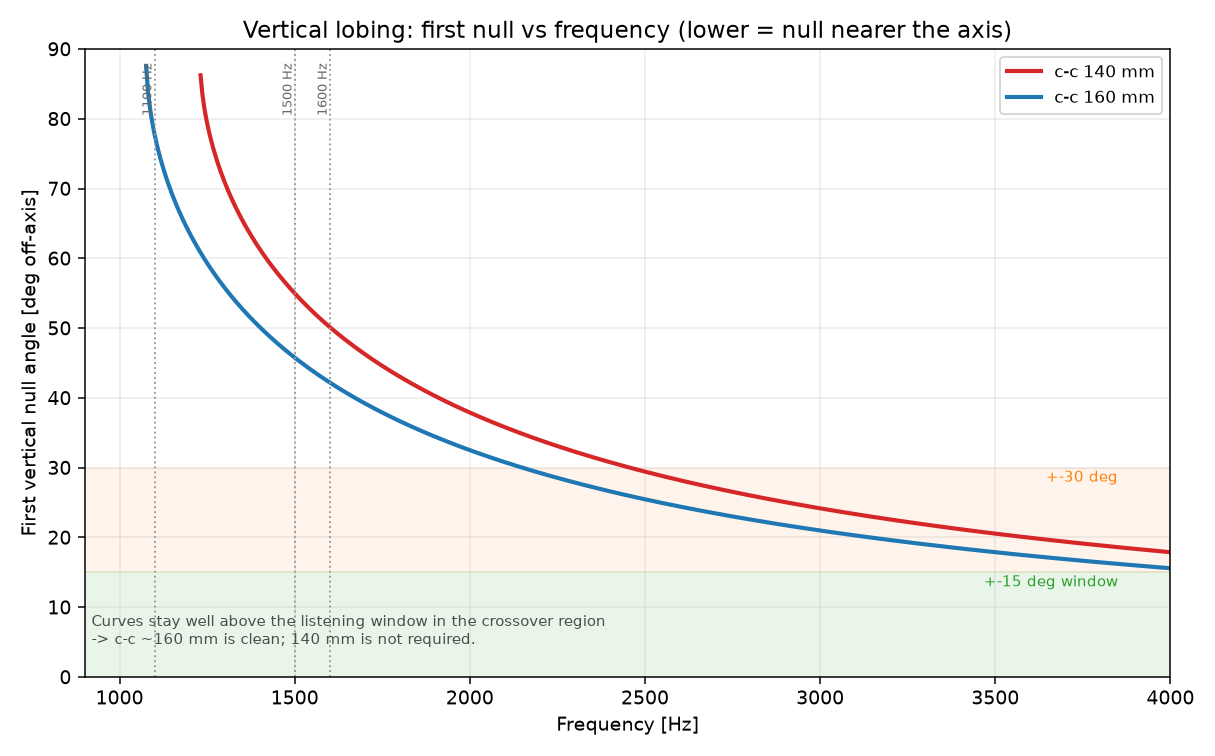
simulations/plots/vertical_lobing.png
