joachimth/mk2-reference-loudspeaker/simulations/plots/vertical_polar_map.png

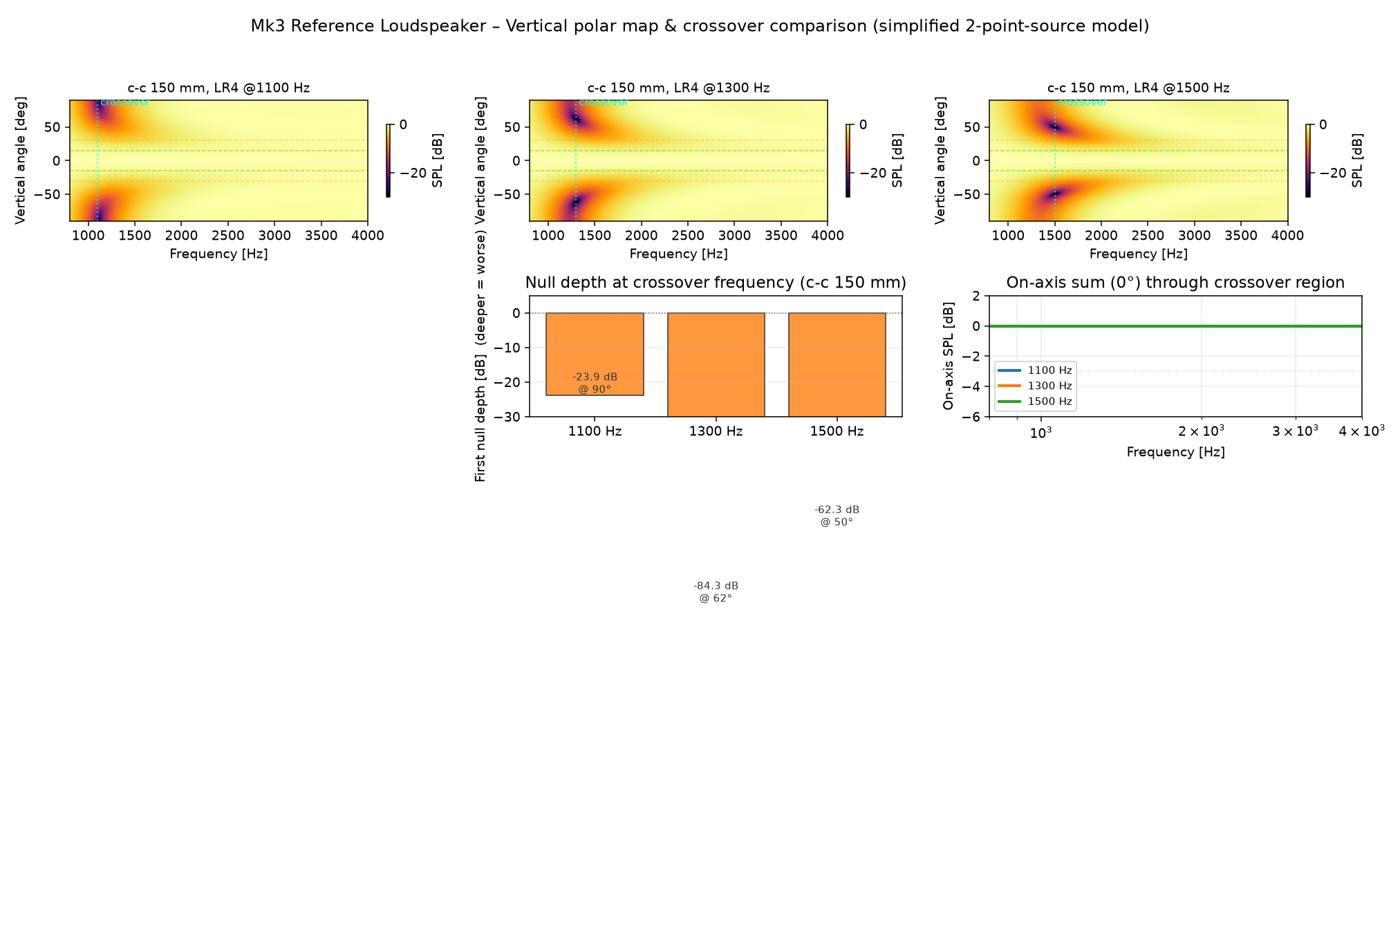
simulations/plots/vertical_polar_map.png
