joachimth/mk2-reference-loudspeaker/assets/renders/waveguide_mouth.png

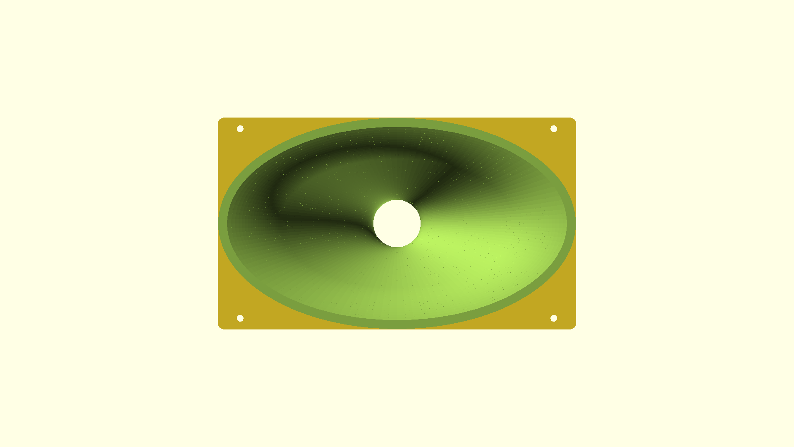
assets/renders/waveguide_mouth.png
