joachimth/mk2-reference-loudspeaker/assets/renders/waveguide_rear.png

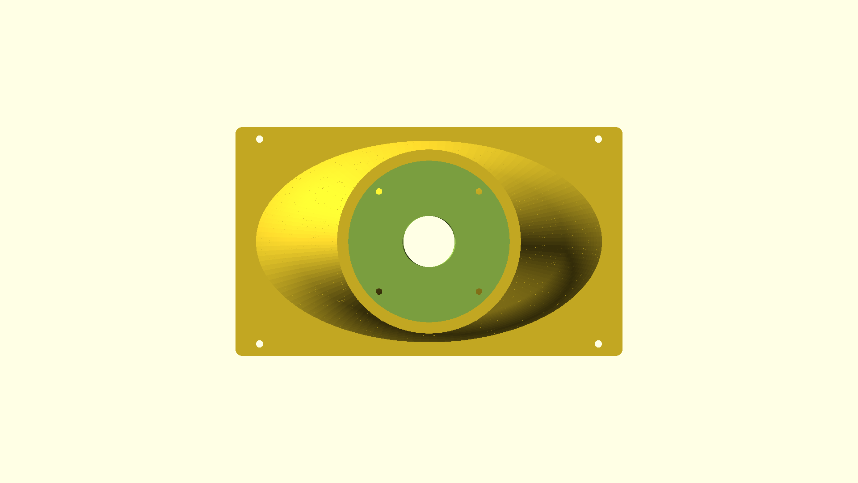
assets/renders/waveguide_rear.png
