joachimth/mk2-reference-loudspeaker/simulations/plots/baffle_step.png

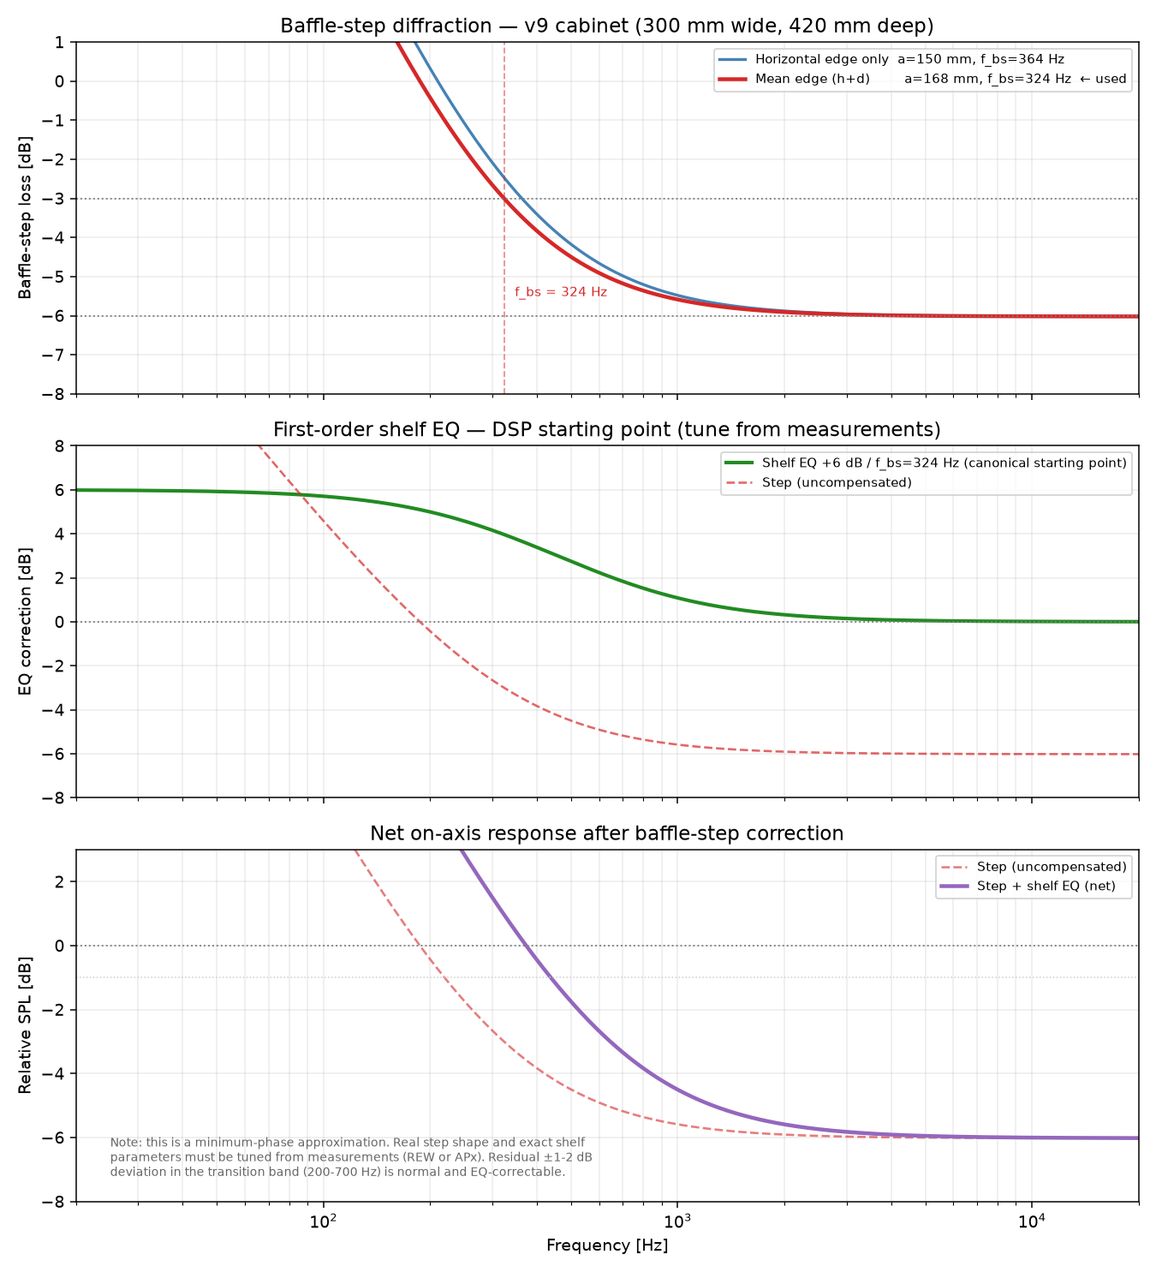
simulations/plots/baffle_step.png
