joachimth/mk2-reference-loudspeaker/simulations/plots/waveguide_termination.png

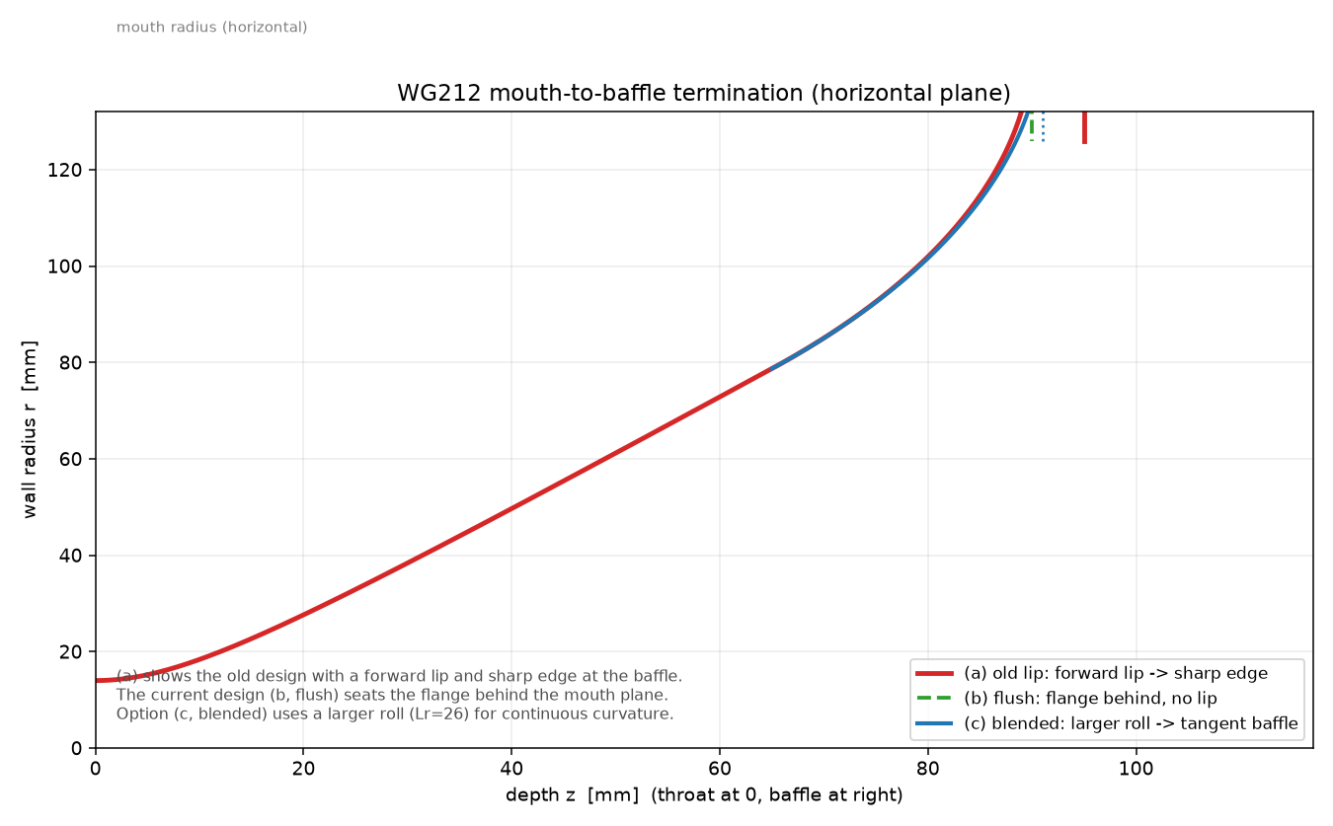
simulations/plots/waveguide_termination.png
